OV-Tech-GmbH/OVT13/01_Electronics/01_Keyboard/KB-PCB-R02/OUTPUT/Layerstack Keyboard_JLCPB.png

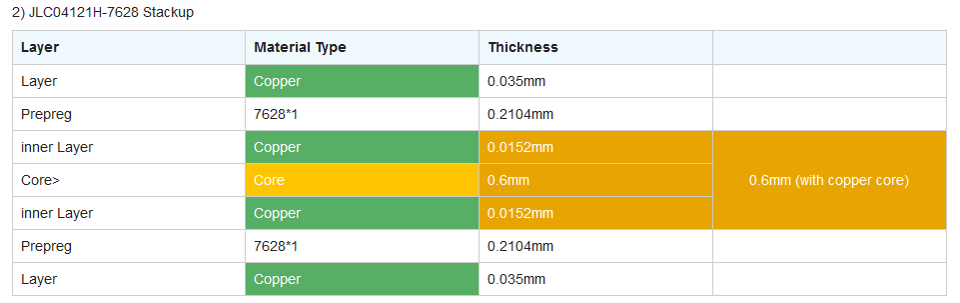
01_Electronics/01_Keyboard/KB-PCB-R02/OUTPUT/Layerstack Keyboard_JLCPB.png
