OV-Tech-GmbH/OVT13/01_Electronics/02_Webcam/KiCad WCAM-TK-PCB-R02/ALTIUM_EMBEDDED_MODELS/ABLS-PCB-R01.stp

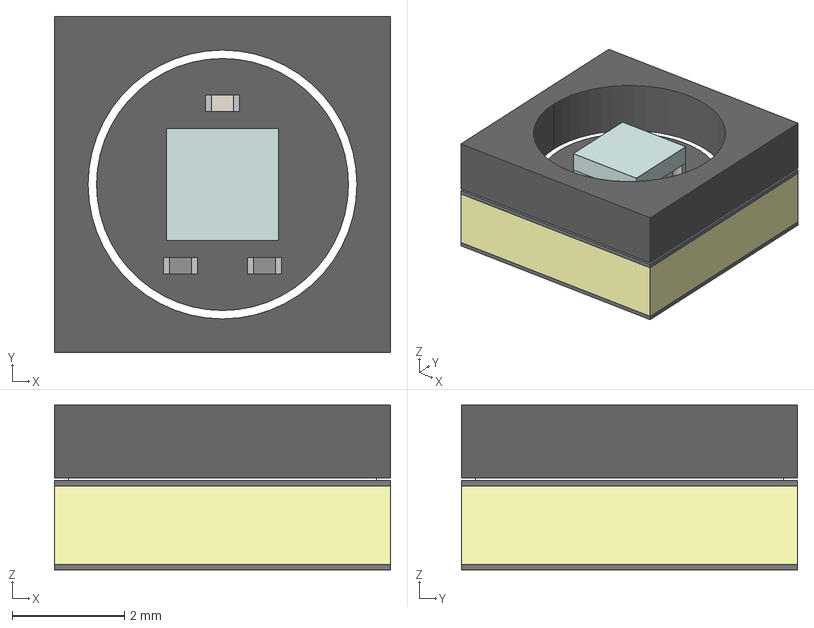
[picture p17: CAD file, 2024-03-24]
01_Electronics/02_Webcam/KiCad WCAM-TK-PCB-R02/ALTIUM_EMBEDDED_MODELS/ABLS-PCB-R01.stp
6.00 x 6.00 x 2.94 mm
ABLS-PCB-R01
IC
Carrier
Verguss
Dampener
