OV-Tech-GmbH/OVT13/01_Electronics/02_Webcam/WCAM-BREAKOUT-PCB-R03/PCB/ALTIUM_EMBEDDED_MODELS/SOT95P275X110-5N.step

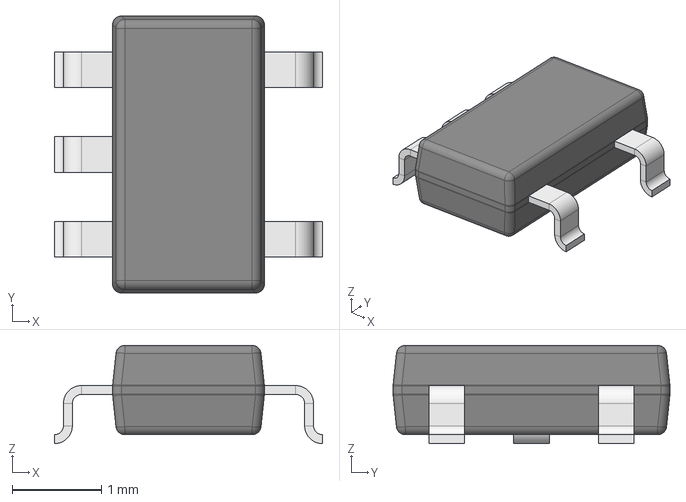
[picture p18: CAD file, 2026-06-02]
01_Electronics/02_Webcam/WCAM-BREAKOUT-PCB-R03/PCB/ALTIUM_EMBEDDED_MODELS/SOT95P275X110-5N.step
3.00 x 3.10 x 1.10 mm
Leader x 5
