OV-Tech-GmbH/OVT13/01_Electronics/02_Webcam/WCAM-TK-PCB-R02/MCAD EXCHANGE/WCAM-PCB-Outline.dxf

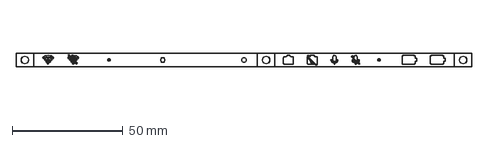
[picture p19: CAD file, 2024-03-02]
01_Electronics/02_Webcam/WCAM-TK-PCB-R02/MCAD EXCHANGE/WCAM-PCB-Outline.dxf
206.0 x 6.00 mm
