OV-Tech-GmbH/OVT13/01_Electronics/03_Trackpad/Trackpad sensor evaluation/TP-EVALBOARD-R01_KiCad/ALTIUM_EMBEDDED_MODELS/USON8_200X300P50.stp

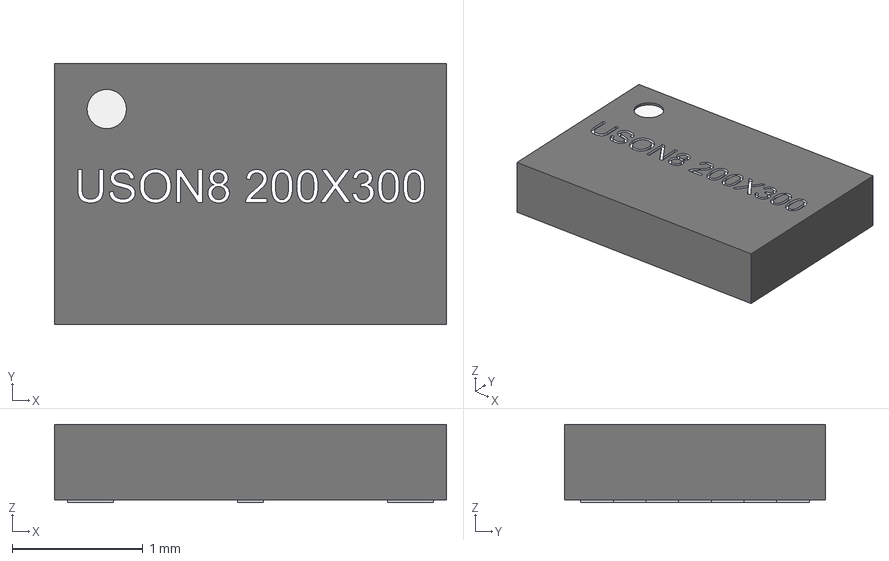
[picture p20: CAD file, 2024-07-25]
01_Electronics/03_Trackpad/Trackpad sensor evaluation/TP-EVALBOARD-R01_KiCad/ALTIUM_EMBEDDED_MODELS/USON8_200X300P50.stp
3.00 x 2.00 x 0.6 mm
