OV-Tech-GmbH/OVT13/01_Electronics/01_Keyboard/KB-PCB-R02_KiCad/ALTIUM_EMBEDDED_MODELS/0603 Chip SMD LED (1.6x0.8mm).STEP

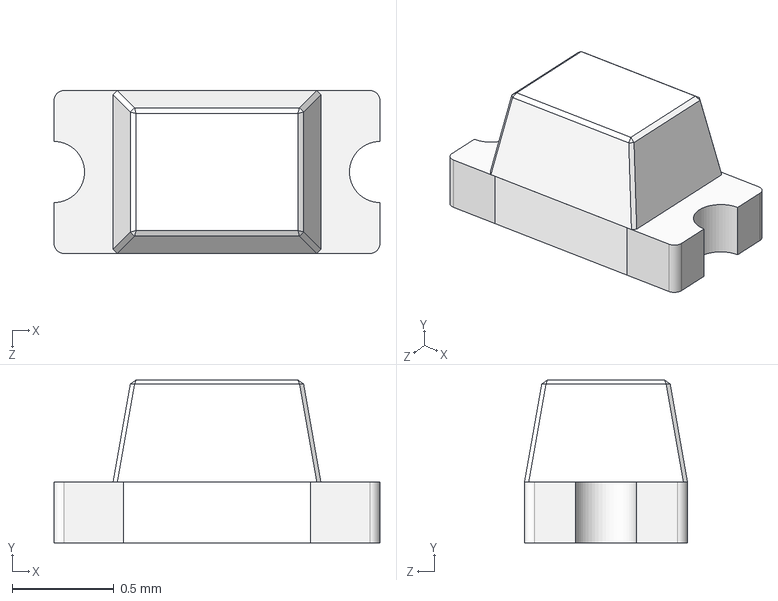
[picture p21: CAD file, 2024-03-24]
01_Electronics/01_Keyboard/KB-PCB-R02_KiCad/ALTIUM_EMBEDDED_MODELS/0603 Chip SMD LED (1.6x0.8mm).STEP
1.60 x 0.8 x 0.8 mm
