OV-Tech-GmbH/OVT13/01_Electronics/02_Webcam/KiCad WCAM-TK-PCB-R02/ALTIUM_EMBEDDED_MODELS/SOT886.stp

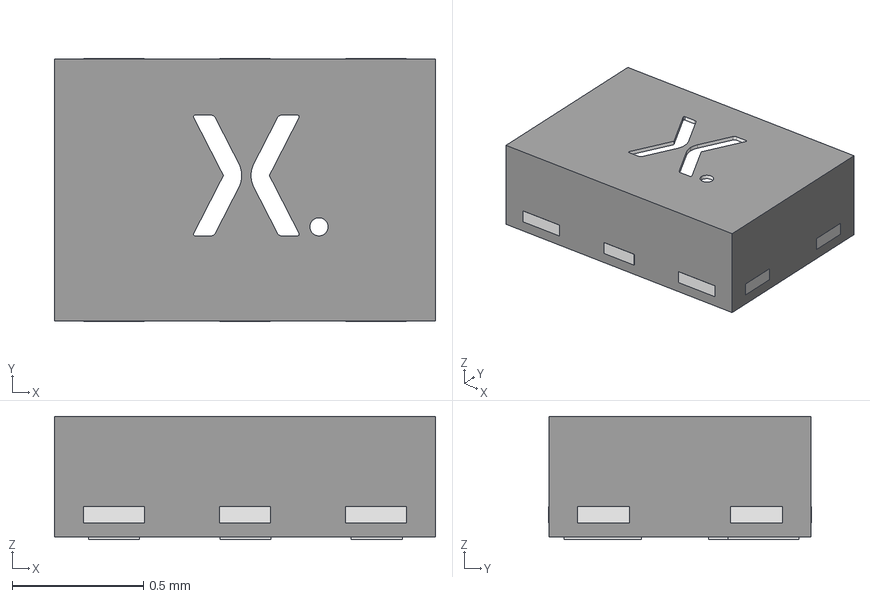
[picture p22: CAD file, 2024-03-24]
01_Electronics/02_Webcam/KiCad WCAM-TK-PCB-R02/ALTIUM_EMBEDDED_MODELS/SOT886.stp
1.45 x 1.00 x 0.47 mm
SOT886 LF
SOT886 Mold Body
