OV-Tech-GmbH/OVT13/01_Electronics/02_Webcam/WCAM-BREAKOUT-PCB-R03/PCB/ALTIUM_EMBEDDED_MODELS/CAF-50P85X64-4N.step

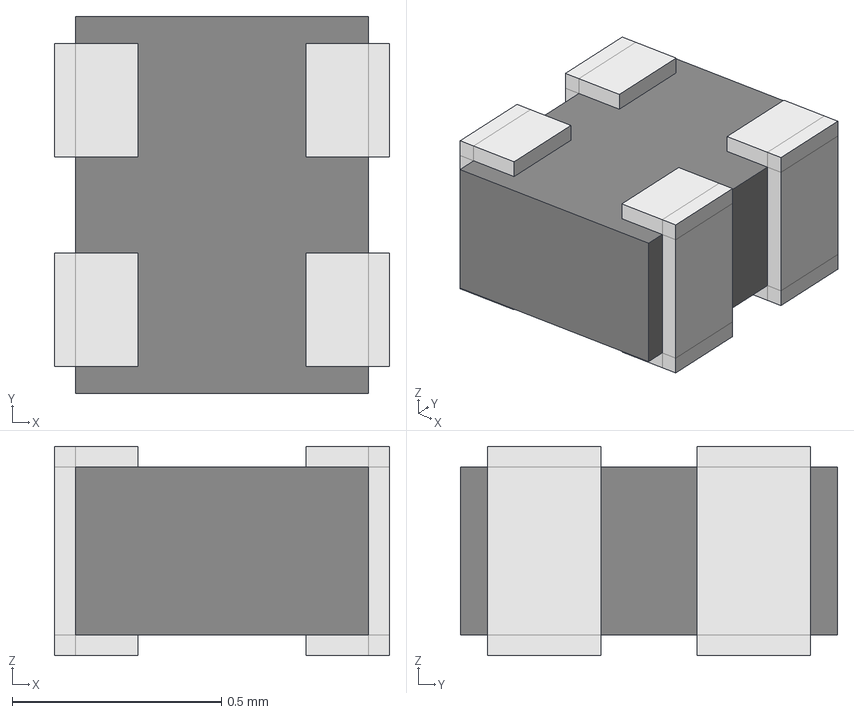
[picture p23: CAD file, 2026-06-02]
01_Electronics/02_Webcam/WCAM-BREAKOUT-PCB-R03/PCB/ALTIUM_EMBEDDED_MODELS/CAF-50P85X64-4N.step
0.8 x 0.9 x 0.5 mm
