OV-Tech-GmbH/OVT13/01_Electronics/03_Trackpad/Trackpad sensor evaluation/TP-EVALBOARD-R01_KiCad/ALTIUM_EMBEDDED_MODELS/Crystal_250X200X60.stp

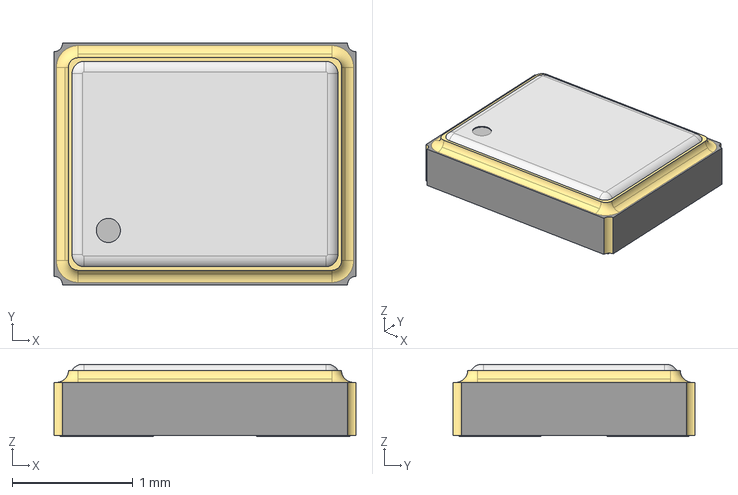
[picture p24: CAD file, 2024-07-25]
01_Electronics/03_Trackpad/Trackpad sensor evaluation/TP-EVALBOARD-R01_KiCad/ALTIUM_EMBEDDED_MODELS/Crystal_250X200X60.stp
2.50 x 2.00 x 0.6 mm
