OV-Tech-GmbH/OVT13/01_Electronics/01_Keyboard/KB-PCB-R02_KiCad/ALTIUM_EMBEDDED_MODELS/MPL-AL4020-xxx.STEP

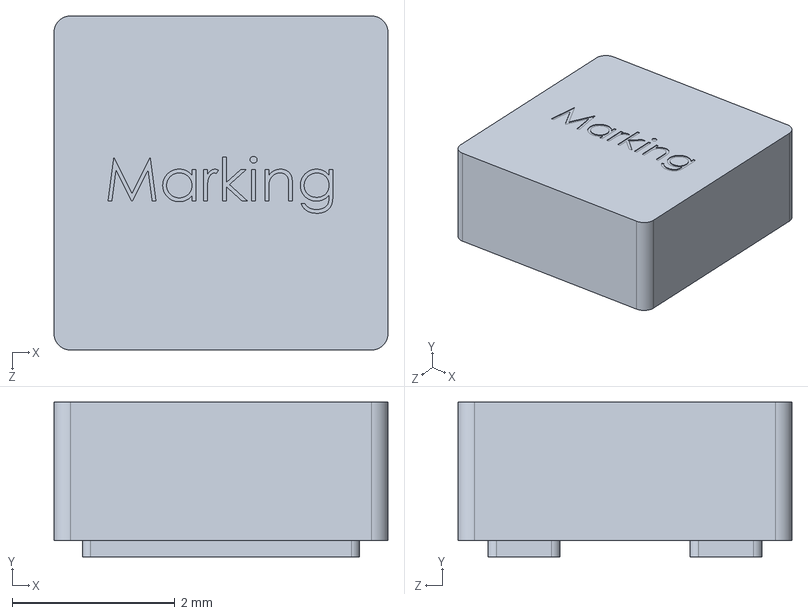
[picture p25: CAD file, 2024-03-24]
01_Electronics/01_Keyboard/KB-PCB-R02_KiCad/ALTIUM_EMBEDDED_MODELS/MPL-AL4020-xxx.STEP
4.10 x 1.90 x 4.10 mm
