OV-Tech-GmbH/OVT13/01_Electronics/02_Webcam/KiCad WCAM-TK-PCB-R02/ALTIUM_EMBEDDED_MODELS/EMI Shielding Spring Contact 3-2199250-3.stp

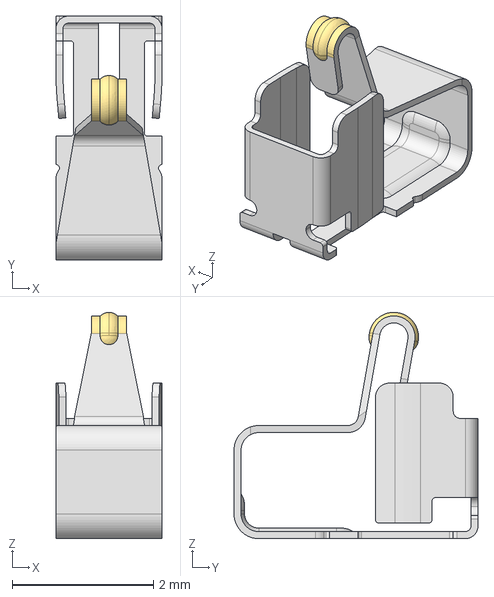
[picture p26: CAD file, 2024-03-24]
01_Electronics/02_Webcam/KiCad WCAM-TK-PCB-R02/ALTIUM_EMBEDDED_MODELS/EMI Shielding Spring Contact 3-2199250-3.stp
1.50 x 3.45 x 3.20 mm
