OV-Tech-GmbH/OVT13/01_Electronics/02_Webcam/WCAM-BREAKOUT-PCB-R03/PCB/ALTIUM_EMBEDDED_MODELS/F32Q-1A7H1-11015--3DModel-STEP-56544.STEP

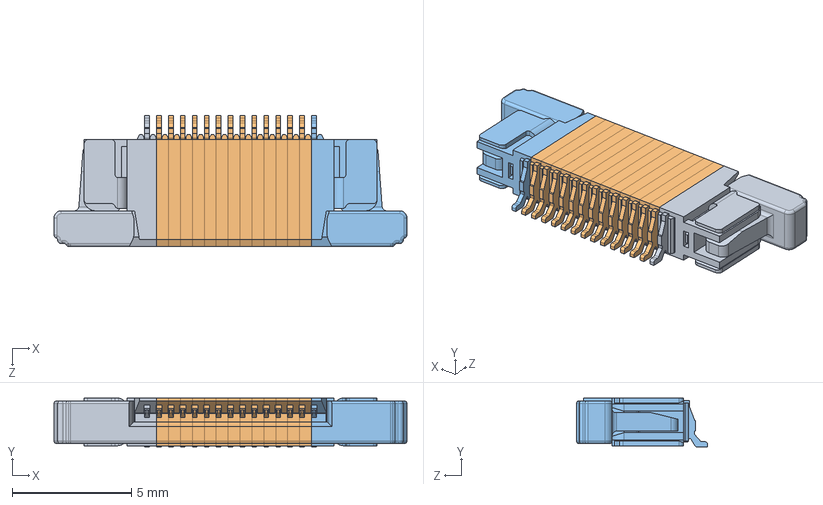
[picture p27: CAD file, 2026-06-02]
01_Electronics/02_Webcam/WCAM-BREAKOUT-PCB-R03/PCB/ALTIUM_EMBEDDED_MODELS/F32Q-1A7H1-11015--3DModel-STEP-56544.STEP
14.8 x 2.05 x 5.50 mm
F32Q_L.STEP
F32Q_M.STEP x 13
F32Q_R.STEP
