OV-Tech-GmbH/OVT13/01_Electronics/03_Trackpad/Trackpad sensor evaluation/TP-EVALBOARD-R01_KiCad/ALTIUM_EMBEDDED_MODELS/PTS815SJM250SMTRLFS.stp

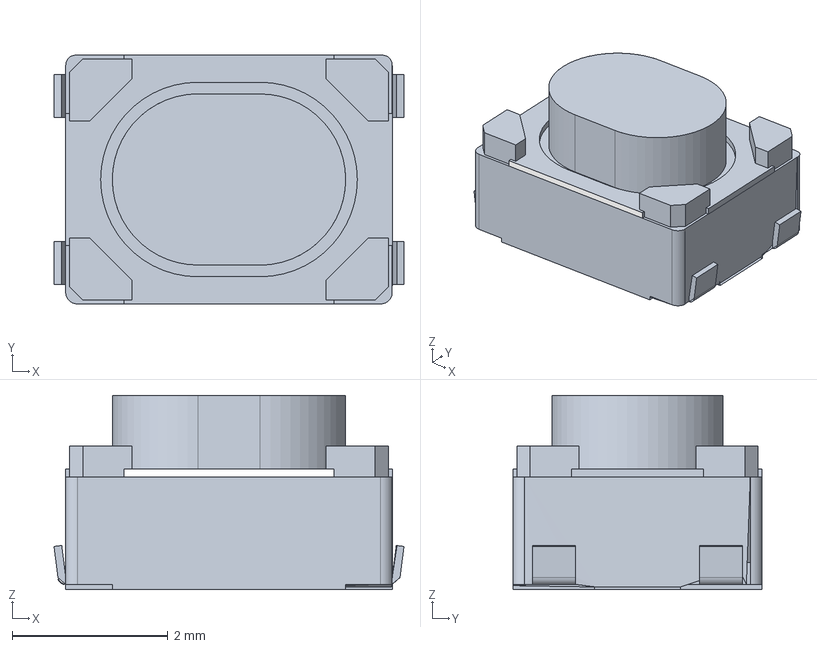
[picture p28: CAD file, 2024-07-25]
01_Electronics/03_Trackpad/Trackpad sensor evaluation/TP-EVALBOARD-R01_KiCad/ALTIUM_EMBEDDED_MODELS/PTS815SJM250SMTRLFS.stp
4.50 x 3.20 x 2.50 mm
PTS815SJM250SMTRLFS_PART3
PTS815SJM250SMTRLFS_PART2
PTS815SJM250SMTRLFS_PART1
