OV-Tech-GmbH/OVT13/01_Electronics/01_Keyboard/KB-PCB-R02_KiCad/ALTIUM_EMBEDDED_MODELS/QFN40P700X700X90_HS-57M.step

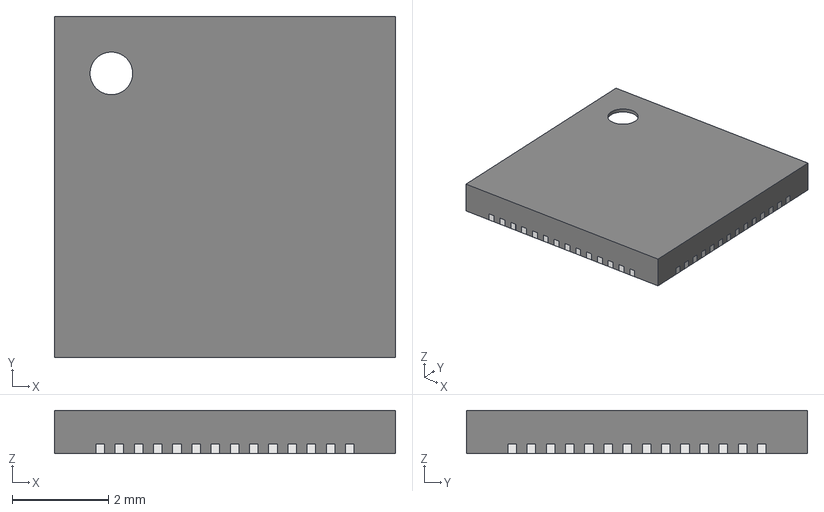
[picture p29: CAD file, 2024-03-24]
01_Electronics/01_Keyboard/KB-PCB-R02_KiCad/ALTIUM_EMBEDDED_MODELS/QFN40P700X700X90_HS-57M.step
7.10 x 7.10 x 0.901 mm
Thermal Shape
