OV-Tech-GmbH/OVT13/01_Electronics/02_Webcam/KiCad WCAM-TK-PCB-R02/ALTIUM_EMBEDDED_MODELS/SOT23-6-2.step

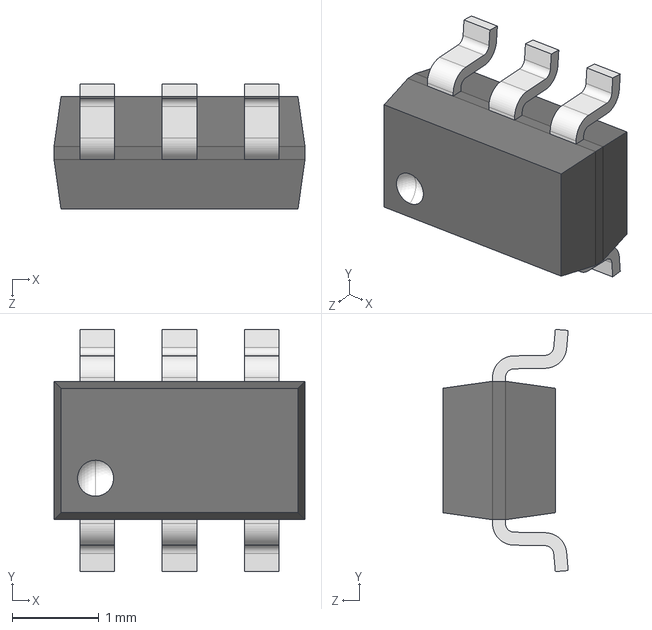
[picture p30: CAD file, 2024-03-24]
01_Electronics/02_Webcam/KiCad WCAM-TK-PCB-R02/ALTIUM_EMBEDDED_MODELS/SOT23-6-2.step
2.90 x 2.80 x 1.45 mm
