OV-Tech-GmbH/OVT13/01_Electronics/02_Webcam/WCAM-BREAKOUT-PCB-R03/PCB/ALTIUM_EMBEDDED_MODELS/TSOP65P280X110-8N.step

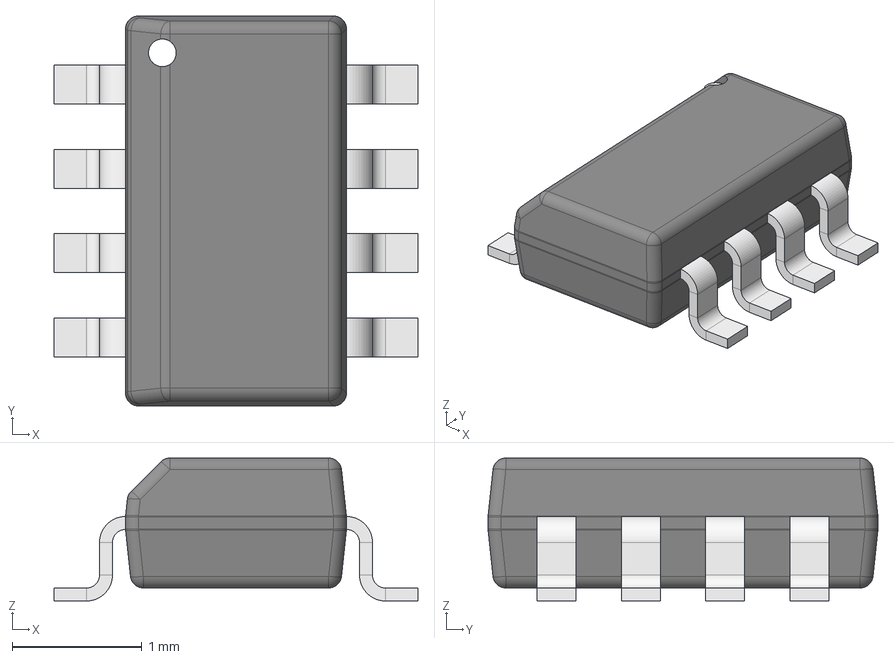
[picture p31: CAD file, 2026-06-02]
01_Electronics/02_Webcam/WCAM-BREAKOUT-PCB-R03/PCB/ALTIUM_EMBEDDED_MODELS/TSOP65P280X110-8N.step
2.80 x 3.00 x 1.10 mm
Leader x 8
