OV-Tech-GmbH/OVT13/01_Electronics/01_Keyboard/KB-PCB-R02_KiCad/ALTIUM_EMBEDDED_MODELS/ECS-143-18-30BQ-DS.STEP

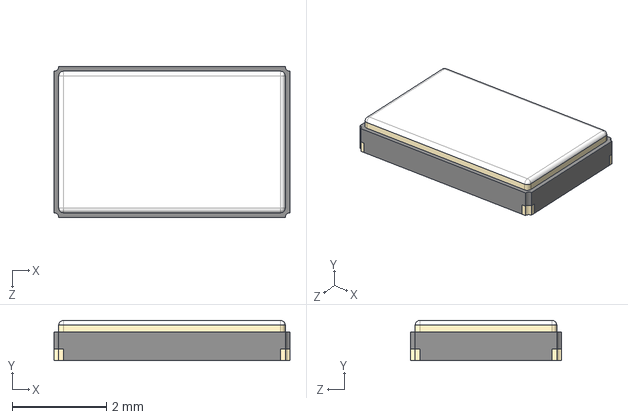
[picture p32: CAD file, 2024-03-24]
01_Electronics/01_Keyboard/KB-PCB-R02_KiCad/ALTIUM_EMBEDDED_MODELS/ECS-143-18-30BQ-DS.STEP
5.00 x 0.85 x 3.20 mm
