OV-Tech-GmbH/OVT13/01_Electronics/02_Webcam/KiCad WCAM-TK-PCB-R02/ALTIUM_EMBEDDED_MODELS/LED_Diffusor.stp

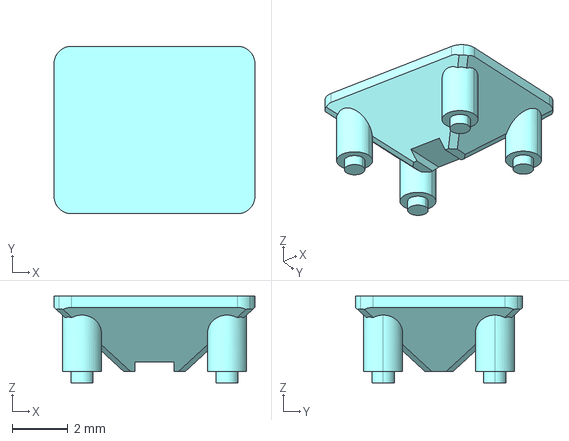
[picture p33: CAD file, 2024-03-24]
01_Electronics/02_Webcam/KiCad WCAM-TK-PCB-R02/ALTIUM_EMBEDDED_MODELS/LED_Diffusor.stp
7.20 x 6.00 x 3.10 mm
