OV-Tech-GmbH/OVT13/01_Electronics/01_Keyboard/KB-PCB-R02_KiCad/ALTIUM_EMBEDDED_MODELS/RES_0603_m1608.stp

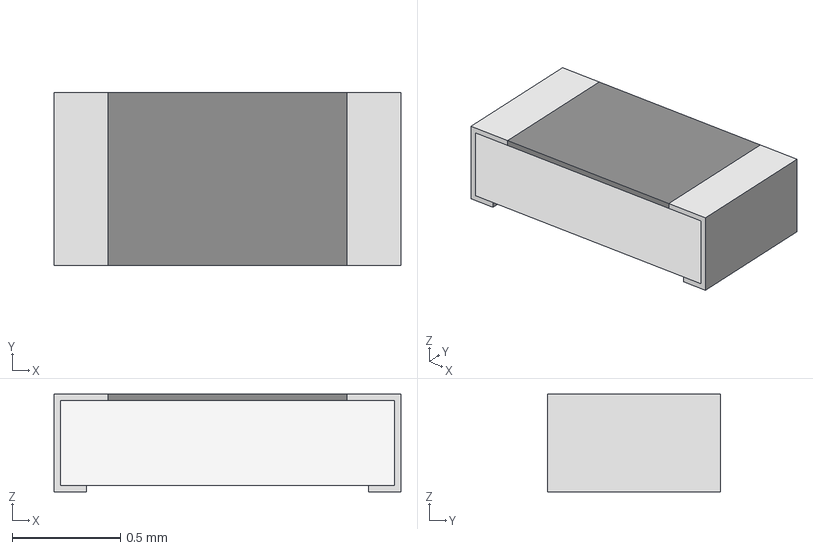
[picture p34: CAD file, 2024-03-24]
01_Electronics/01_Keyboard/KB-PCB-R02_KiCad/ALTIUM_EMBEDDED_MODELS/RES_0603_m1608.stp
1.60 x 0.8 x 0.45 mm
