OV-Tech-GmbH/OVT13/01_Electronics/02_Webcam/KiCad WCAM-TK-PCB-R02/ALTIUM_EMBEDDED_MODELS/WCAM-MOUNT-PCB-R01.step

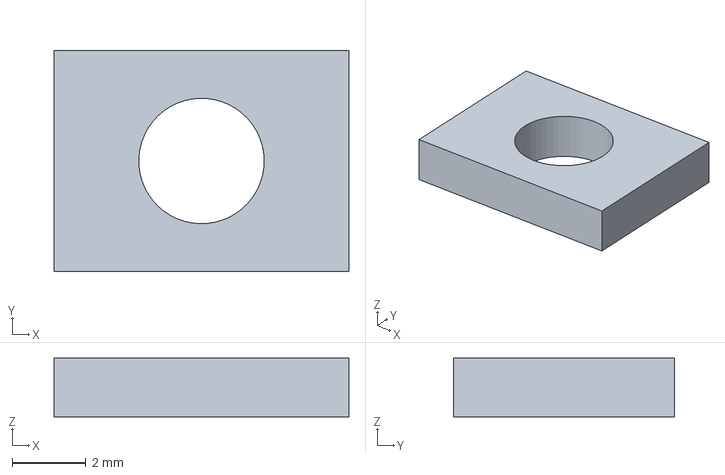
[picture p35: CAD file, 2024-03-02]
01_Electronics/02_Webcam/KiCad WCAM-TK-PCB-R02/ALTIUM_EMBEDDED_MODELS/WCAM-MOUNT-PCB-R01.step
8.00 x 6.00 x 1.59 mm
