OV-Tech-GmbH/OVT13/01_Electronics/03_Trackpad/Trackpad sensor evaluation/TP-EVALBOARD-R01_KiCad/ALTIUM_EMBEDDED_MODELS/User Library-JST - SM05B-SRSS-TB (SH SERIES - 1_0mm PITCH WIRE-TO-BOARD, SMT, RA).step

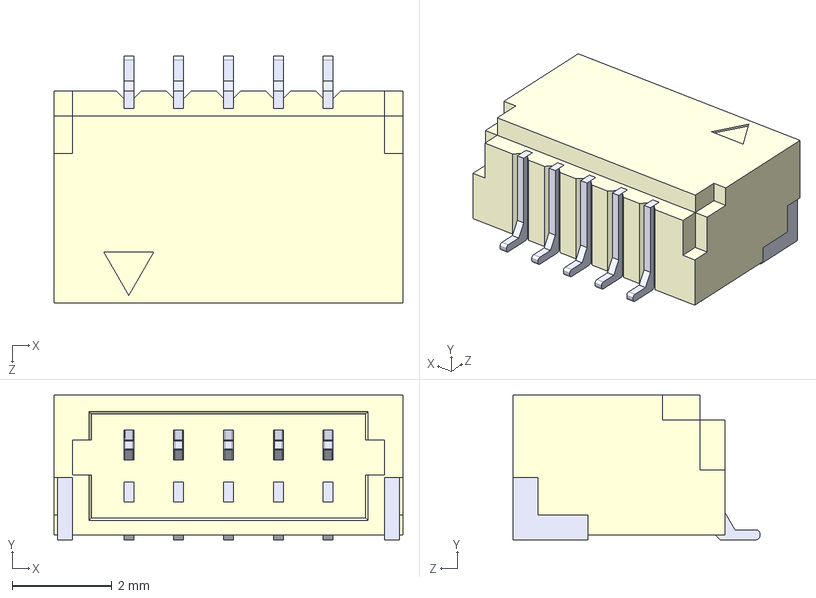
[picture p36: CAD file, 2024-03-24]
01_Electronics/03_Trackpad/Trackpad sensor evaluation/TP-EVALBOARD-R01_KiCad/ALTIUM_EMBEDDED_MODELS/User Library-JST - SM05B-SRSS-TB (SH SERIES - 1_0mm PITCH WIRE-TO-BOARD, SMT, RA).step
7.00 x 2.90 x 4.95 mm
