OV-Tech-GmbH/OVT13/01_Electronics/02_Webcam/KiCad WCAM-TK-PCB-R02/ALTIUM_EMBEDDED_MODELS/3D Model Mic Dampener.stp

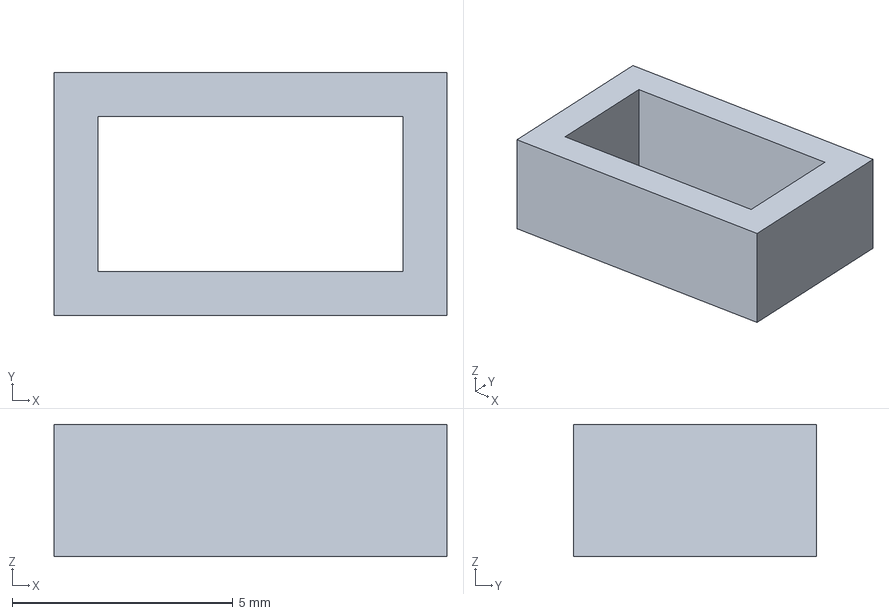
[picture p37: CAD file, 2024-03-02]
01_Electronics/02_Webcam/KiCad WCAM-TK-PCB-R02/ALTIUM_EMBEDDED_MODELS/3D Model Mic Dampener.stp
8.90 x 5.50 x 3.00 mm
