OV-Tech-GmbH/OVT13/01_Electronics/02_Webcam/WCAM-BREAKOUT-PCB-R03/PCB/ALTIUM_EMBEDDED_MODELS/X2SON 1x1x0.4.stp

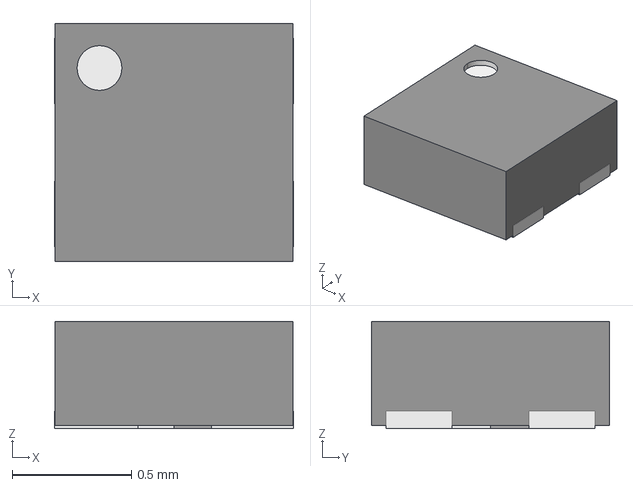
[picture p38: CAD file, 2024-03-24]
01_Electronics/02_Webcam/WCAM-BREAKOUT-PCB-R03/PCB/ALTIUM_EMBEDDED_MODELS/X2SON 1x1x0.4.stp
1.00 x 1.00 x 0.45 mm
