OV-Tech-GmbH/OVT13/01_Electronics/03_Trackpad/Trackpad sensor evaluation/TP-EVALBOARD-R01_KiCad/ALTIUM_EMBEDDED_MODELS/CAP_0603_m1608.stp

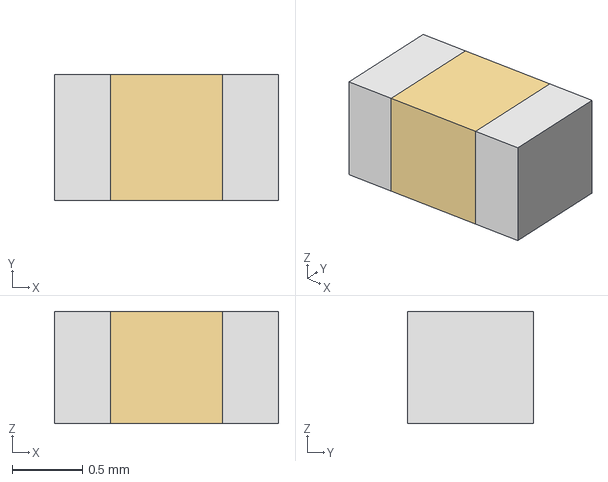
[picture p39: CAD file, 2024-03-24]
01_Electronics/03_Trackpad/Trackpad sensor evaluation/TP-EVALBOARD-R01_KiCad/ALTIUM_EMBEDDED_MODELS/CAP_0603_m1608.stp
1.60 x 0.9 x 0.8 mm
