OV-Tech-GmbH/OVT13/01_Electronics/01_Keyboard/KB-PCB-R02_KiCad/ALTIUM_EMBEDDED_MODELS/CPG1316S01D02.2.stp

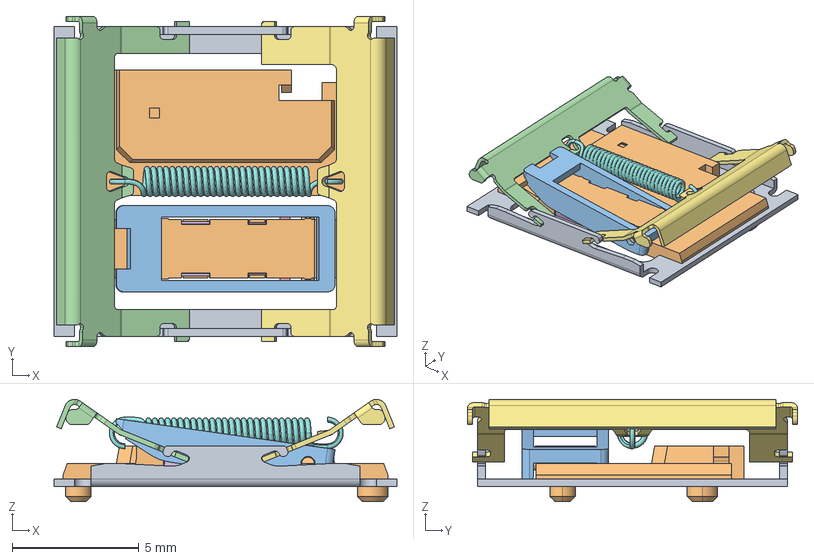
[picture p40: CAD file, 2024-03-24]
01_Electronics/01_Keyboard/KB-PCB-R02_KiCad/ALTIUM_EMBEDDED_MODELS/CPG1316S01D02.2.stp
13.5 x 13.0 x 4.03 mm
Base
Base_Plastic
Switch_Lever
Lever_2
Stabilizer_1
Stabilizer_2
Lever_1
Spring
