OV-Tech-GmbH/OVT13/01_Electronics/02_Webcam/WCAM-BREAKOUT-PCB-R03/PCB/ALTIUM_EMBEDDED_MODELS/Image Sensor OV2740.stp

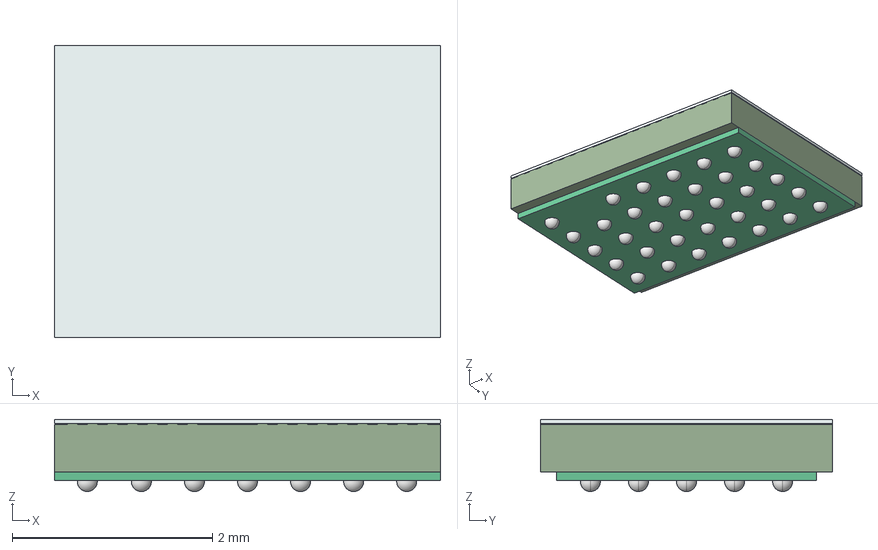
[picture p41: CAD file, 2024-03-24]
01_Electronics/02_Webcam/WCAM-BREAKOUT-PCB-R03/PCB/ALTIUM_EMBEDDED_MODELS/Image Sensor OV2740.stp
3.85 x 2.92 x 0.72 mm
Cover
Base
Balls
