OV-Tech-GmbH/OVT13/01_Electronics/01_Keyboard/KB-PCB-R02_KiCad/ALTIUM_EMBEDDED_MODELS/SON50P300X60_HS-9N.step

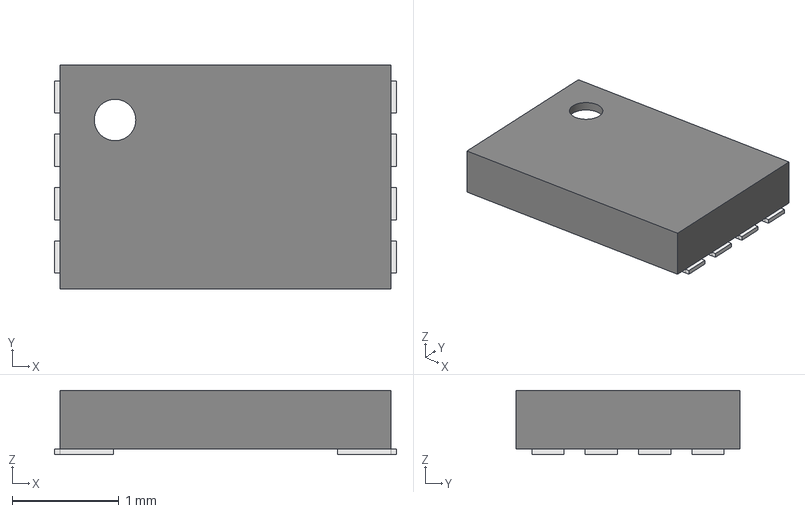
[picture p42: CAD file, 2024-03-24]
01_Electronics/01_Keyboard/KB-PCB-R02_KiCad/ALTIUM_EMBEDDED_MODELS/SON50P300X60_HS-9N.step
3.20 x 2.10 x 0.6 mm
