OV-Tech-GmbH/OVT13/01_Electronics/02_Webcam/WCAM-BREAKOUT-PCB-R03/PCB/ALTIUM_EMBEDDED_MODELS/Oscillator ECS-2520MV.stp

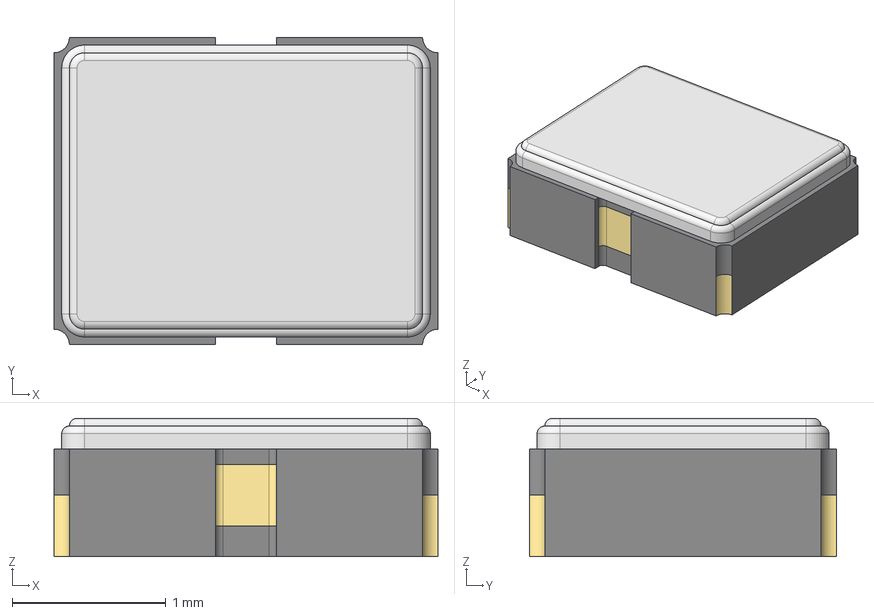
[picture p43: CAD file, 2024-03-24]
01_Electronics/02_Webcam/WCAM-BREAKOUT-PCB-R03/PCB/ALTIUM_EMBEDDED_MODELS/Oscillator ECS-2520MV.stp
2.50 x 2.00 x 0.9 mm
