OV-Tech-GmbH/OVT13/01_Electronics/02_Webcam/WCAM-BREAKOUT-PCB-R03/PCB/ALTIUM_EMBEDDED_MODELS/DFN65P98X50-3N.step

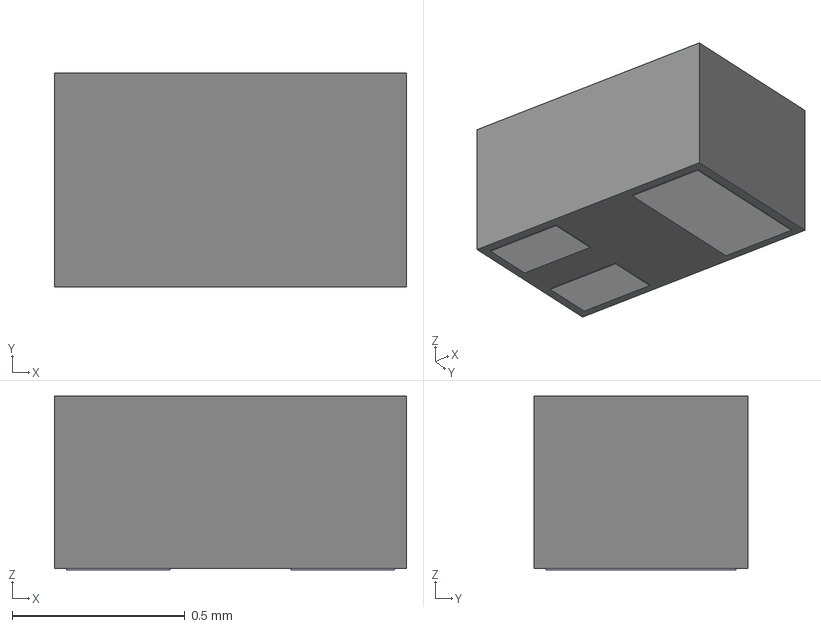
[picture p44: CAD file, 2024-03-24]
01_Electronics/02_Webcam/WCAM-BREAKOUT-PCB-R03/PCB/ALTIUM_EMBEDDED_MODELS/DFN65P98X50-3N.step
1.02 x 0.62 x 0.503 mm
bigPin
smallPine x 2
