OV-Tech-GmbH/OVT13/01_Electronics/02_Webcam/WCAM-BREAKOUT-PCB-R03/PCB/ALTIUM_EMBEDDED_MODELS/DFN65P100X50-2N.step

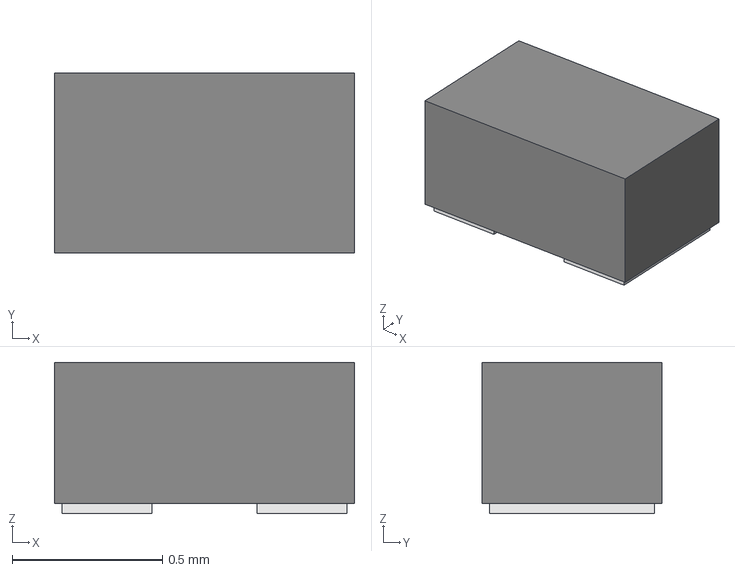
[picture p45: CAD file, 2024-03-24]
01_Electronics/02_Webcam/WCAM-BREAKOUT-PCB-R03/PCB/ALTIUM_EMBEDDED_MODELS/DFN65P100X50-2N.step
1.00 x 0.6 x 0.503 mm
bigPin x 2
