OV-Tech-GmbH/OVT13/01_Electronics/02_Webcam/WCAM-BREAKOUT-PCB-R01/OUTPUT/Lagenaufbau Keyboard_JLCPB.png

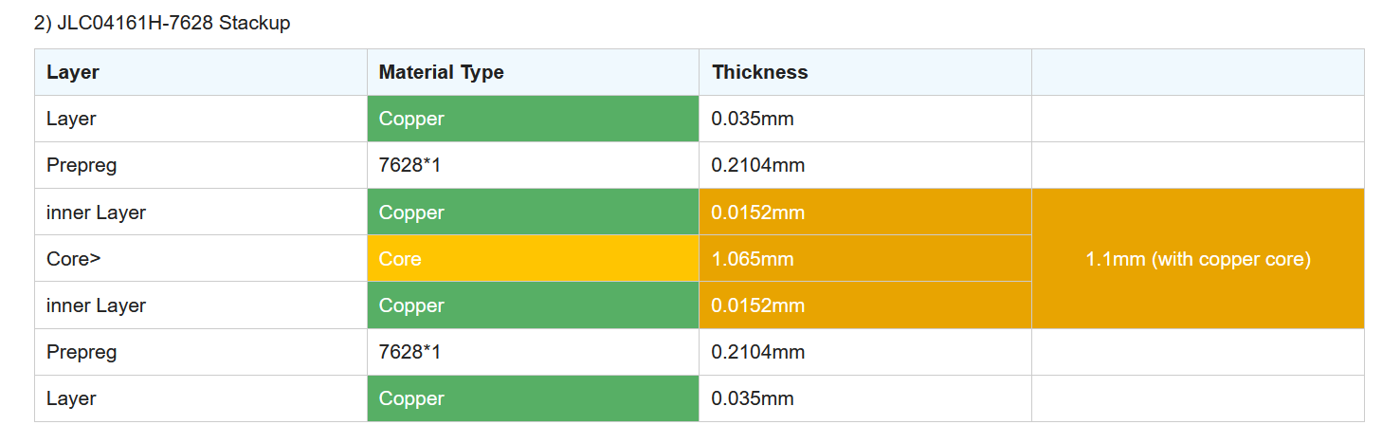
01_Electronics/02_Webcam/WCAM-BREAKOUT-PCB-R01/OUTPUT/Lagenaufbau Keyboard_JLCPB.png
