OV-Tech-GmbH/OVT13/01_Electronics/01_Keyboard/KB-PCB-R02_KiCad/Input_MCU.kicad_sch

## KiCad design 01_Electronics/01_Keyboard/KB-PCB-R02_KiCad/Input_MCU.kicad_sch (2024-03-24)

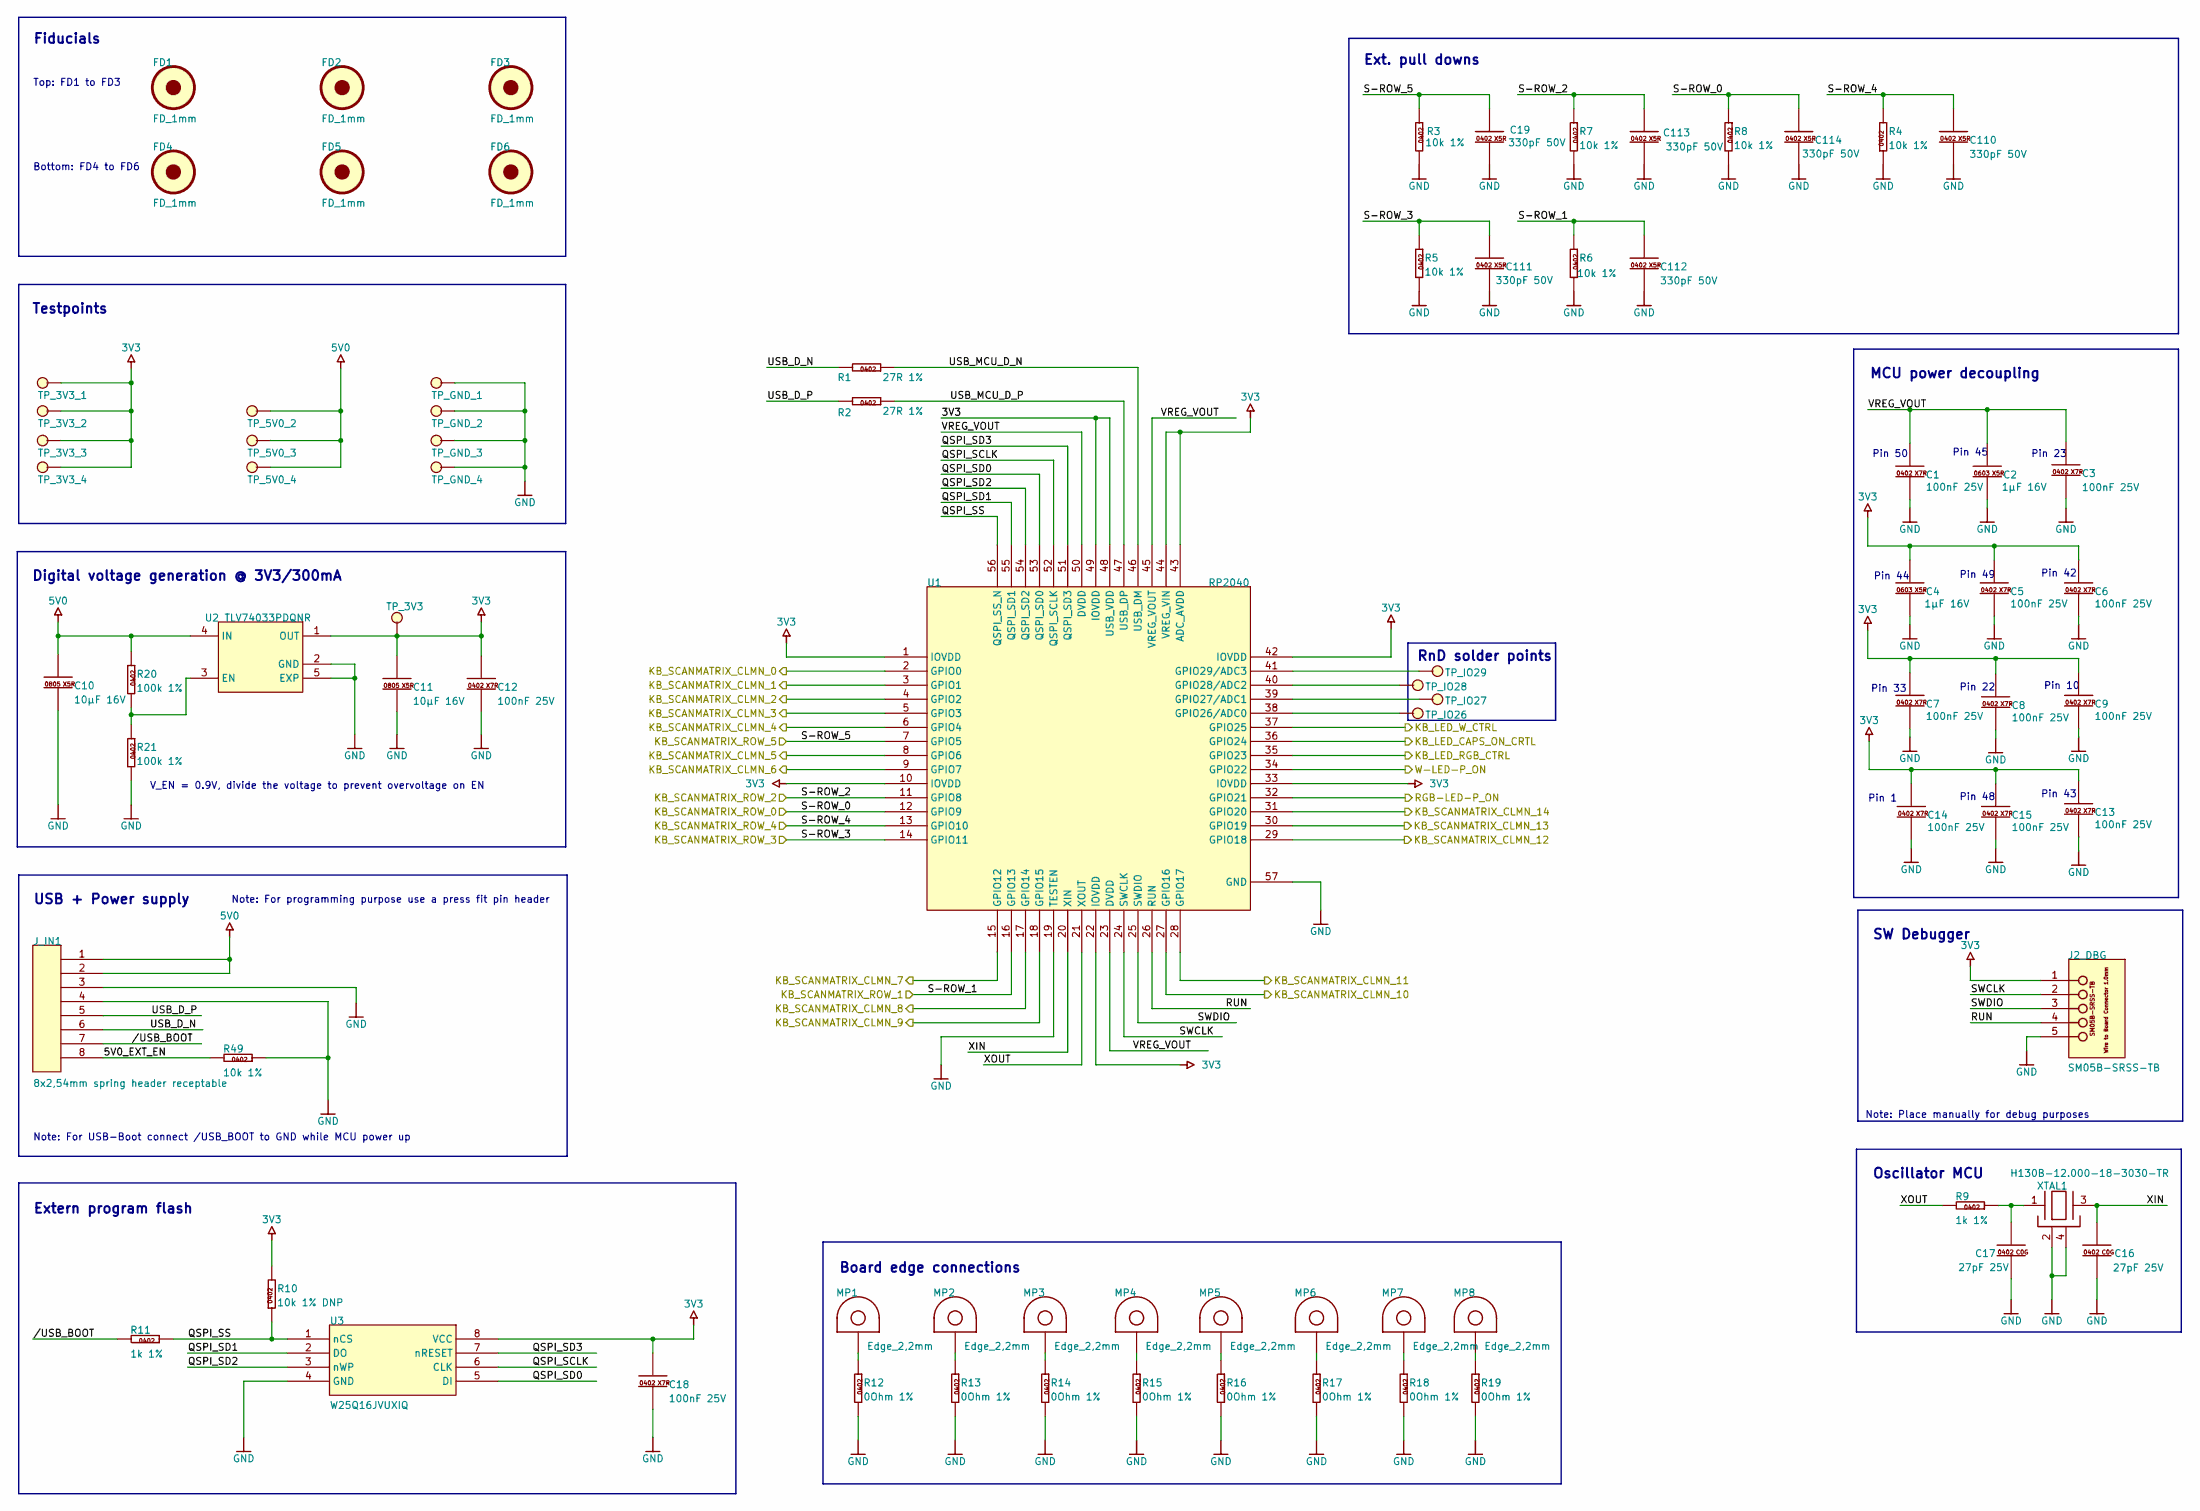
[picture p61: schematic Input_MCU.kicad_sch]

Parts:
C1, C3, C5, C6, C7, C8, C9, C12, C13, C14, C15, C18: 100nF 25V; CAPC1005X06L
C2, C4: 1µF 16V; CAPC1608X10L
C10, C11: 10µF 16V; CAPC2012X14L
C16, C17: 27pF 25V; CAPC1005X06L
C19, C110, C111, C112, C113, C114: 330pF 50V; CAPC1005X06L
FD1, FD2, FD3, FD4, FD5, FD6: FD_1mm; FD_1mm_Copper_3mm_Expansion
J2_DBG: SM05B-SRSS-TB; Wire-to-Board SM05B-SRSS-TB
J_IN1: 8x2,54mm spring header receptable; BOARD-BOARD CON SPRING-LOADED HEADER 8x2,54mm Receptable; MANUFACTURER PART NUMBE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 N/A
MP1, MP2, MP3, MP4, MP5, MP6, MP7, MP8: Edge_2,2mm; MP_Keyboard_EdgeMounts_2.2mm
R1, R2: 27R 1%; RESC1005X04L
R3, R4, R5, R6, R7, R8, R49: 10k 1%; RESC1005X04L
R9, R11: 1k 1%; RESC1005X04L
R10: 10k 1% DNP; RESC1005X04L
R12, R13, R14, R15, R16, R17, R18, R19: 0Ohm 1%; RESC1005X04L
R20, R21: 100k 1%; RESC1005X04L
TP_3V3, TP_3V3_1, TP_3V3_2, TP_3V3_3, TP_3V3_4, TP_5V0_2, TP_5V0_3, TP_5V0_4: Testpoint 0.75mm; TP_0.75mm
TP_GND_1, TP_GND_2, TP_GND_3, TP_GND_4: Testpoint 0.75mm; TP_0.75mm
TP_IO26, TP_IO27, TP_IO28, TP_IO29: Testpoint 0.75mm; TP_0.75mm
U1: RP2040; QFN40P700X700X90_HS-57M
U2: TLV74033PDQNR; X2SON-DFN
U3: W25Q16JVUXIQ; SON50P300X60_HS-9N; MANUFACTURER PART NUMBE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 W25Q16JVUXIQ
XTAL1: H130B-12.000-18-3030-TR; XTAL_H130B-12.000-18-3030-TR

Connections:
3V3: U1.48 (USB_VDD), U1.49 (IOVDD)
5V0_EXT_EN: J_IN1.8, R49.1
/USB_BOOT: J_IN1.7, R11.1
KB_LED_CAPS_ON_CRTL: U1.36 (GPIO24)
KB_LED_RGB_CTRL: U1.35 (GPIO23)
KB_LED_W_CTRL: U1.37 (GPIO25)
KB_SCANMATRIX_CLMN_0: U1.2 (GPIO0)
KB_SCANMATRIX_CLMN_1: C19.1, C111.1, R3.2, R5.2, U1.3 (GPIO1), U1.4 (GPIO2), U1.5 (GPIO3), U1.7 (GPIO5), U1.9 (GPIO7), U1.14 (GPIO11), U1.15 (GPIO12), U1.17 (GPIO14), U1.18 (GPIO15)
KB_SCANMATRIX_CLMN_4: U1.6 (GPIO4)
KB_SCANMATRIX_CLMN_5: U1.8 (GPIO6)
KB_SCANMATRIX_CLMN_10: U1.27 (GPIO16)
KB_SCANMATRIX_CLMN_11: U1.28 (GPIO17)
KB_SCANMATRIX_CLMN_12: U1.29 (GPIO18)
KB_SCANMATRIX_CLMN_13: U1.30 (GPIO19)
KB_SCANMATRIX_CLMN_14: U1.31 (GPIO20)
KB_SCANMATRIX_ROW_0: C114.1, R8.2, U1.12 (GPIO9)
KB_SCANMATRIX_ROW_1: C112.1, R6.2, U1.16 (GPIO13)
KB_SCANMATRIX_ROW_2: C113.1, R7.2, U1.11 (GPIO8)
KB_SCANMATRIX_ROW_4: C110.1, R4.1, U1.13 (GPIO10)
unnamed: C4.1, C5.1, C6.1
unnamed: C7.1, C8.1, C9.1
unnamed: C10.1, R20.2, U2.4 (IN)
unnamed: C11.1, C12.1, TP_3V3.TP, U2.1 (OUT)
unnamed: C13.1, C14.1, C15.1
unnamed: C17.1, R9.2, XTAL1.1
unnamed: C18.1, U3.8 (VCC)
unnamed: J_IN1.1, J_IN1.2
unnamed: J_IN1.4, R49.2
unnamed: MP1.1, R12.2
unnamed: MP2.1, R13.2
unnamed: MP3.1, R14.2
unnamed: MP4.1, R15.2
unnamed: MP5.1, R16.2
unnamed: MP6.1, R17.2
unnamed: MP7.1, R18.2
unnamed: MP8.1, R19.2
unnamed: R20.1, R21.2, U2.3 (EN)
unnamed: TP_3V3_1.TP, TP_3V3_2.TP, TP_3V3_3.TP, TP_3V3_4.TP
unnamed: TP_5V0_2.TP, TP_5V0_3.TP, TP_5V0_4.TP
unnamed: TP_GND_1.TP, TP_GND_2.TP, TP_GND_3.TP, TP_GND_4.TP
unnamed: TP_IO26.TP, U1.38 (GPIO26/ADC0)
unnamed: TP_IO27.TP, U1.39 (GPIO27/ADC1)
unnamed: TP_IO28.TP, U1.40 (GPIO28/ADC2)
unnamed: TP_IO29.TP, U1.41 (GPIO29/ADC3)
unnamed: U1.43 (ADC_AVDD), U1.44 (VREG_VIN)
unnamed: U2.2 (GND), U2.5 (EXP)
unnamed: XTAL1.2, XTAL1.4
QSPI_SCLK: U1.52 (QSPI_SCLK), U3.6 (CLK)
QSPI_SD0: U1.53 (QSPI_SD0), U3.5 (DI)
QSPI_SD1: U1.55 (QSPI_SD1), U3.2 (DO)
QSPI_SD2: U1.54 (QSPI_SD2), U3.3 (nWP)
QSPI_SD3: U1.51 (QSPI_SD3), U3.7 (nRESET)
QSPI_SS: R10.2, R11.2, U1.56 (QSPI_SS_N), U3.1 (nCS)
RGB-LED-P_ON: U1.32 (GPIO21)
RUN: J2_DBG.4, U1.26 (RUN)
SWCLK: J2_DBG.2, U1.24 (SWCLK)
SWDIO: J2_DBG.3, U1.25 (SWDIO)
USB_D_N: J_IN1.6, R1.1
USB_D_P: J_IN1.5, R2.1
USB_MCU_D_N: R1.2, U1.46 (USB_DM)
USB_MCU_D_P: R2.2, U1.47 (USB_DP)
VREG_VOUT: C1.1, C2.1, C3.1, U1.23 (DVDD), U1.45 (VREG_VOUT), U1.50 (DVDD)
W-LED-P_ON: U1.34 (GPIO22)
XIN: C16.1, U1.20 (XIN), XTAL1.3
XOUT: R9.1, U1.21 (XOUT)

Notes on the sheet:
Note: For USB-Boot connect /USB_BOOT to GND while MCU power up
Pin 22
USB + Power supply
Top: FD1 to FD3
Pin 49
Pin 33
V_EN = 0.9V, divide the voltage to prevent overvoltage on EN
Note: For programming purpose use a press fit pin header
Pin 48
Ext. pull downs
Board edge connections
Bottom: FD4 to FD6
Testpoints
Pin 23
Pin 44
Extern program flash
Pin 1
Pin 45
Note: Place manually for debug purposes
Pin 42
Pin 43
MCU power decoupling
SW Debugger
Pin 10
Pin 50
RnD solder points
Fiducials
Oscillator MCU
Digital voltage generation @ 3V3/300mA
