OV-Tech-GmbH/OVT13/01_Electronics/01_Keyboard/KB-PCB-R02_KiCad/Keymatrix_switches.kicad_sch

## KiCad design 01_Electronics/01_Keyboard/KB-PCB-R02_KiCad/Keymatrix_switches.kicad_sch (2024-03-24)

Schematic: Keymatrix_switches.kicad_sch

Parts:
D1, D2, D3, D4, D5, D6, D7, D8, D9, D10, D11, D12, D13, D14, D15, D16, D17, D18, D19, D20, D21, D22, D23, D24, D25, D26, D27, D28, D29, D30, D31, D32, D33, D34, D35, D36, D37, D38, D39, D40, D41, D42, D43, D44, D45, D46, D47, D48, D49, D50, D51, D52, D53, D54, D55, D56, D57, D58, D59, D60, D61, D62, D63, D64, D65, D66, D67, D68, D69, D70, D71, D72, D73, D74, D75, D76, D77, D78, D79, D80: BAT54LS-QYL; DFN1006-2A
D81, D82, D83, D84, D85, D86, D87, D88, D89, D90, D91, D92, D93, D94, D95, D96, D97, D98, D99, D100, D101: PESD5V5C1UL; DFN65P100X50-2N
R147, R148, R149, R150, R151, R152, R153, R154, R155, R156, R157, R158, R159, R160, R161, R162, R163, R164, R165, R166, R167: 300R 1%; RESC1005X04L
SW1, SW2, SW3, SW4, SW5, SW6, SW7, SW8, SW9, SW10, SW11, SW12, SW13, SW14, SW15, SW16, SW17, SW18, SW19, SW20, SW21, SW22, SW23, SW24, SW25, SW26, SW27, SW28, SW29, SW30, SW31, SW32, SW33, SW34, SW35, SW36, SW37, SW38, SW39, SW40, SW41, SW42, SW43, SW44, SW45, SW46, SW47, SW48, SW49, SW50, SW51, SW52, SW53, SW54, SW55, SW56, SW57, SW58, SW59, SW60, SW61, SW62, SW63, SW64, SW65, SW66, SW67, SW68, SW69, SW70, SW71, SW72, SW73, SW74, SW75, SW76, SW77, SW78, SW79, SW80, SW81: CPG1316S01D02; SW_KEYBOARD_KAIHL-PG1316S

Connections:
KB_SCANMATRIX_CLMN_0: R147.2
KB_SCANMATRIX_CLMN_1: R148.2
KB_SCANMATRIX_CLMN_2: R149.2, R150.2
KB_SCANMATRIX_CLMN_4: R151.2
KB_SCANMATRIX_CLMN_5: R152.2
KB_SCANMATRIX_CLMN_6: R153.2
KB_SCANMATRIX_CLMN_7: R154.2
KB_SCANMATRIX_CLMN_8: R155.2
KB_SCANMATRIX_CLMN_9: R156.2
KB_SCANMATRIX_CLMN_10: R157.2
KB_SCANMATRIX_CLMN_11: R158.2
KB_SCANMATRIX_CLMN_12: R159.2
KB_SCANMATRIX_CLMN_13: R160.2
KB_SCANMATRIX_CLMN_14: R161.2
KB_SCANMATRIX_ROW_0: R162.1
KB_SCANMATRIX_ROW_1: R163.1
KB_SCANMATRIX_ROW_2: R164.1
KB_SCANMATRIX_ROW_3: R165.1
KB_SCANMATRIX_ROW_4: R166.1
KB_SCANMATRIX_ROW_5: R167.1
unnamed: D1.1, D2.1, D3.1, D4.1, D5.1, D6.1, D7.1, D8.1, D9.1, D10.1, D11.1, D12.1, D13.1, D14.1, D15.1, D96.1, R162.2
unnamed: D1.2, SW1.2
unnamed: D2.2, SW2.2
unnamed: D3.2, SW3.2
unnamed: D4.2, SW4.2
unnamed: D5.2, SW5.2
unnamed: D6.2, SW6.2
unnamed: D7.2, SW7.2
unnamed: D8.2, SW8.2
unnamed: D9.2, SW9.2
unnamed: D10.2, SW10.2
unnamed: D11.2, SW11.2
unnamed: D12.2, SW12.2
unnamed: D13.2, SW13.2
unnamed: D14.2, SW14.2
unnamed: D15.2, SW15.2
unnamed: D16.1, D17.1, D18.1, D19.1, D20.1, D21.1, D22.1, D23.1, D24.1, D25.1, D26.1, D27.1, D28.1, D29.1, D97.1, R163.2
unnamed: D16.2, SW16.2
unnamed: D17.2, SW17.2
unnamed: D18.2, SW18.2
unnamed: D19.2, SW19.2
unnamed: D20.2, SW20.2
unnamed: D21.2, SW21.2
unnamed: D22.2, SW22.2
unnamed: D23.2, SW23.2
unnamed: D24.2, SW24.2
unnamed: D25.2, SW25.2
unnamed: D26.2, SW26.2
unnamed: D27.2, SW27.2
unnamed: D28.2, SW28.2
unnamed: D29.2, SW29.2
unnamed: D30.1, D31.1, D32.1, D33.1, D34.1, D35.1, D36.1, D37.1, D38.1, D39.1, D40.1, D41.1, D42.1, D43.1, D98.1, R164.2
unnamed: D30.2, SW30.2
unnamed: D31.2, SW31.2
unnamed: D32.2, SW32.2
unnamed: D33.2, SW33.2
unnamed: D34.2, SW34.2
unnamed: D35.2, SW35.2
unnamed: D36.2, SW36.2
unnamed: D37.2, SW37.2
unnamed: D38.2, SW38.2
unnamed: D39.2, SW39.2
unnamed: D40.2, SW40.2
unnamed: D41.2, SW41.2
unnamed: D42.2, SW42.2
unnamed: D43.2, SW43.2
unnamed: D44.1, D45.1, D46.1, D47.1, D48.1, D49.1, D50.1, D51.1, D52.1, D53.1, D54.1, D55.1, D56.1, D99.1, R165.2
unnamed: D44.2, SW44.2
unnamed: D45.2, SW45.2
unnamed: D46.2, SW46.2
unnamed: D47.2, SW47.2
unnamed: D48.2, SW48.2
unnamed: D49.2, SW49.2
unnamed: D50.2, SW50.2
unnamed: D51.2, SW51.2
unnamed: D52.2, SW52.2
unnamed: D53.2, SW53.2
unnamed: D54.2, SW54.2
unnamed: D55.2, SW55.2
unnamed: D56.2, SW56.2
unnamed: D57.2, SW57.2
unnamed: D58.2, SW58.2
unnamed: D59.2, SW59.2
unnamed: D60.2, SW60.2
unnamed: D61.2, SW61.2
unnamed: D62.2, SW62.2
unnamed: D63.2, SW63.2
unnamed: D64.2, SW64.2
unnamed: D65.2, SW65.2
unnamed: D66.2, SW66.2
unnamed: D67.2, SW67.2
unnamed: D68.2, SW68.2
unnamed: D69.2, SW69.2
unnamed: D70.2, SW70.2
unnamed: D71.2, SW71.2
unnamed: D72.2, SW72.2
unnamed: D73.2, SW73.2
unnamed: D74.2, SW74.2, SW75.2
unnamed: D75.2, SW76.2
unnamed: D76.2, SW77.2
unnamed: D77.2, SW78.2
unnamed: D78.2, SW79.2
unnamed: D79.2, SW80.2
unnamed: D80.2, SW81.2
unnamed: D81.1, R147.1, SW1.1, SW16.1, SW30.1, SW44.1, SW57.1, SW70.1
unnamed: D82.1, R148.1, SW2.1, SW17.1, SW31.1, SW45.1, SW58.1, SW71.1
unnamed: D83.1, R149.1, SW3.1, SW18.1, SW32.1, SW46.1, SW59.1, SW72.1
unnamed: D84.1, R150.1, SW4.1, SW19.1, SW33.1, SW47.1, SW60.1, SW73.1
unnamed: D85.1, R151.1, SW5.1, SW20.1, SW34.1, SW48.1, SW61.1
unnamed: D86.1, R152.1, SW6.1, SW21.1, SW35.1, SW49.1, SW62.1, SW74.1, SW75.1
unnamed: D87.1, R153.1, SW7.1, SW22.1, SW36.1, SW50.1, SW63.1
unnamed: D88.1, R154.1, SW8.1, SW23.1, SW37.1, SW51.1, SW64.1
unnamed: D89.1, R155.1, SW9.1, SW24.1, SW38.1, SW52.1, SW65.1, SW76.1
unnamed: D90.1, R156.1, SW10.1, SW25.1, SW39.1, SW53.1, SW66.1, SW77.1
unnamed: D91.1, R157.1, SW11.1, SW26.1, SW40.1, SW54.1, SW67.1, SW78.1
unnamed: D92.1, R158.1, SW12.1, SW27.1, SW41.1, SW55.1, SW68.1, SW79.1
unnamed: D93.1, R159.1, SW13.1, SW28.1, SW42.1, SW56.1, SW69.1, SW80.1
unnamed: D94.1, R160.1, SW14.1, SW29.1, SW81.1
unnamed: D95.1, R161.1, SW15.1, SW43.1
unnamed: D57.1, D58.1, D59.1, D60.1, D61.1, D62.1, D63.1, D64.1, D65.1, D66.1, D67.1, D68.1, D69.1, D100.1, R166.2
unnamed: D70.1, D71.1, D72.1, D73.1, D74.1, D75.1, D76.1, D77.1, D78.1, D79.1, D80.1, D101.1, R167.2

Notes on the sheet:
KC_P
KC_UP
KC_M
Keycode alignment based on QWERTY layout (eng)
KC_F7
KC_F1
KC_F8
KC_I
KC_S
KC_7
KC_8
KC_CAPS_LOCK
KC_F9
KC_1
KC_U
KC_F6
KC_H
KC_C
KC_4
KC_TAB
KC_9
KC_Y
KC_RIGHT_BRACKET
KC_F12
KC_RIGHT_CTRL
KC_F2
KC_F5
KC_X
KC_F4
KC_6
KC_R
KC_BACKSLASH
KC_SEMICOLON
KC_RIGHT
KC_ENTER
KC_F
KC_LEFT_ALT
KC_T
KC_E
KC_3
KC_N
KC_F11
KC_A
KC_LEFT_SHIFT
KC_ESCAPE
KC_2
KC_DELETE
KC_GRAVE
KC_RIGHT_ALT
KC_SLASH
KC_LEFT_BRACKET
KC_F10
KC_NONUS_HASH
KC_EQUAL
KC_B
KC_J
KC_COMMA
KC_QUOTE
KC_G
KC_F3
KC_O
KC_LEFT
MO(layer)
KC_DOWN
KC_LEFT_CTRL
KC_Z
KC_Q
KC_RIGHT_SHIFT
KC_DOT
KC_L
KC_0
KC_SPACE
KC_D
KC_NO
Specific keyfunctions being implemented in the firmware
KC_W
KC_5
KC_V
KC_K
KC_INSERT
