OV-Tech-GmbH/OVT13/01_Electronics/01_Keyboard/KB-PCB-R02_KiCad/backlight_RGB.kicad_sch

## KiCad design 01_Electronics/01_Keyboard/KB-PCB-R02_KiCad/backlight_RGB.kicad_sch (2024-03-24)

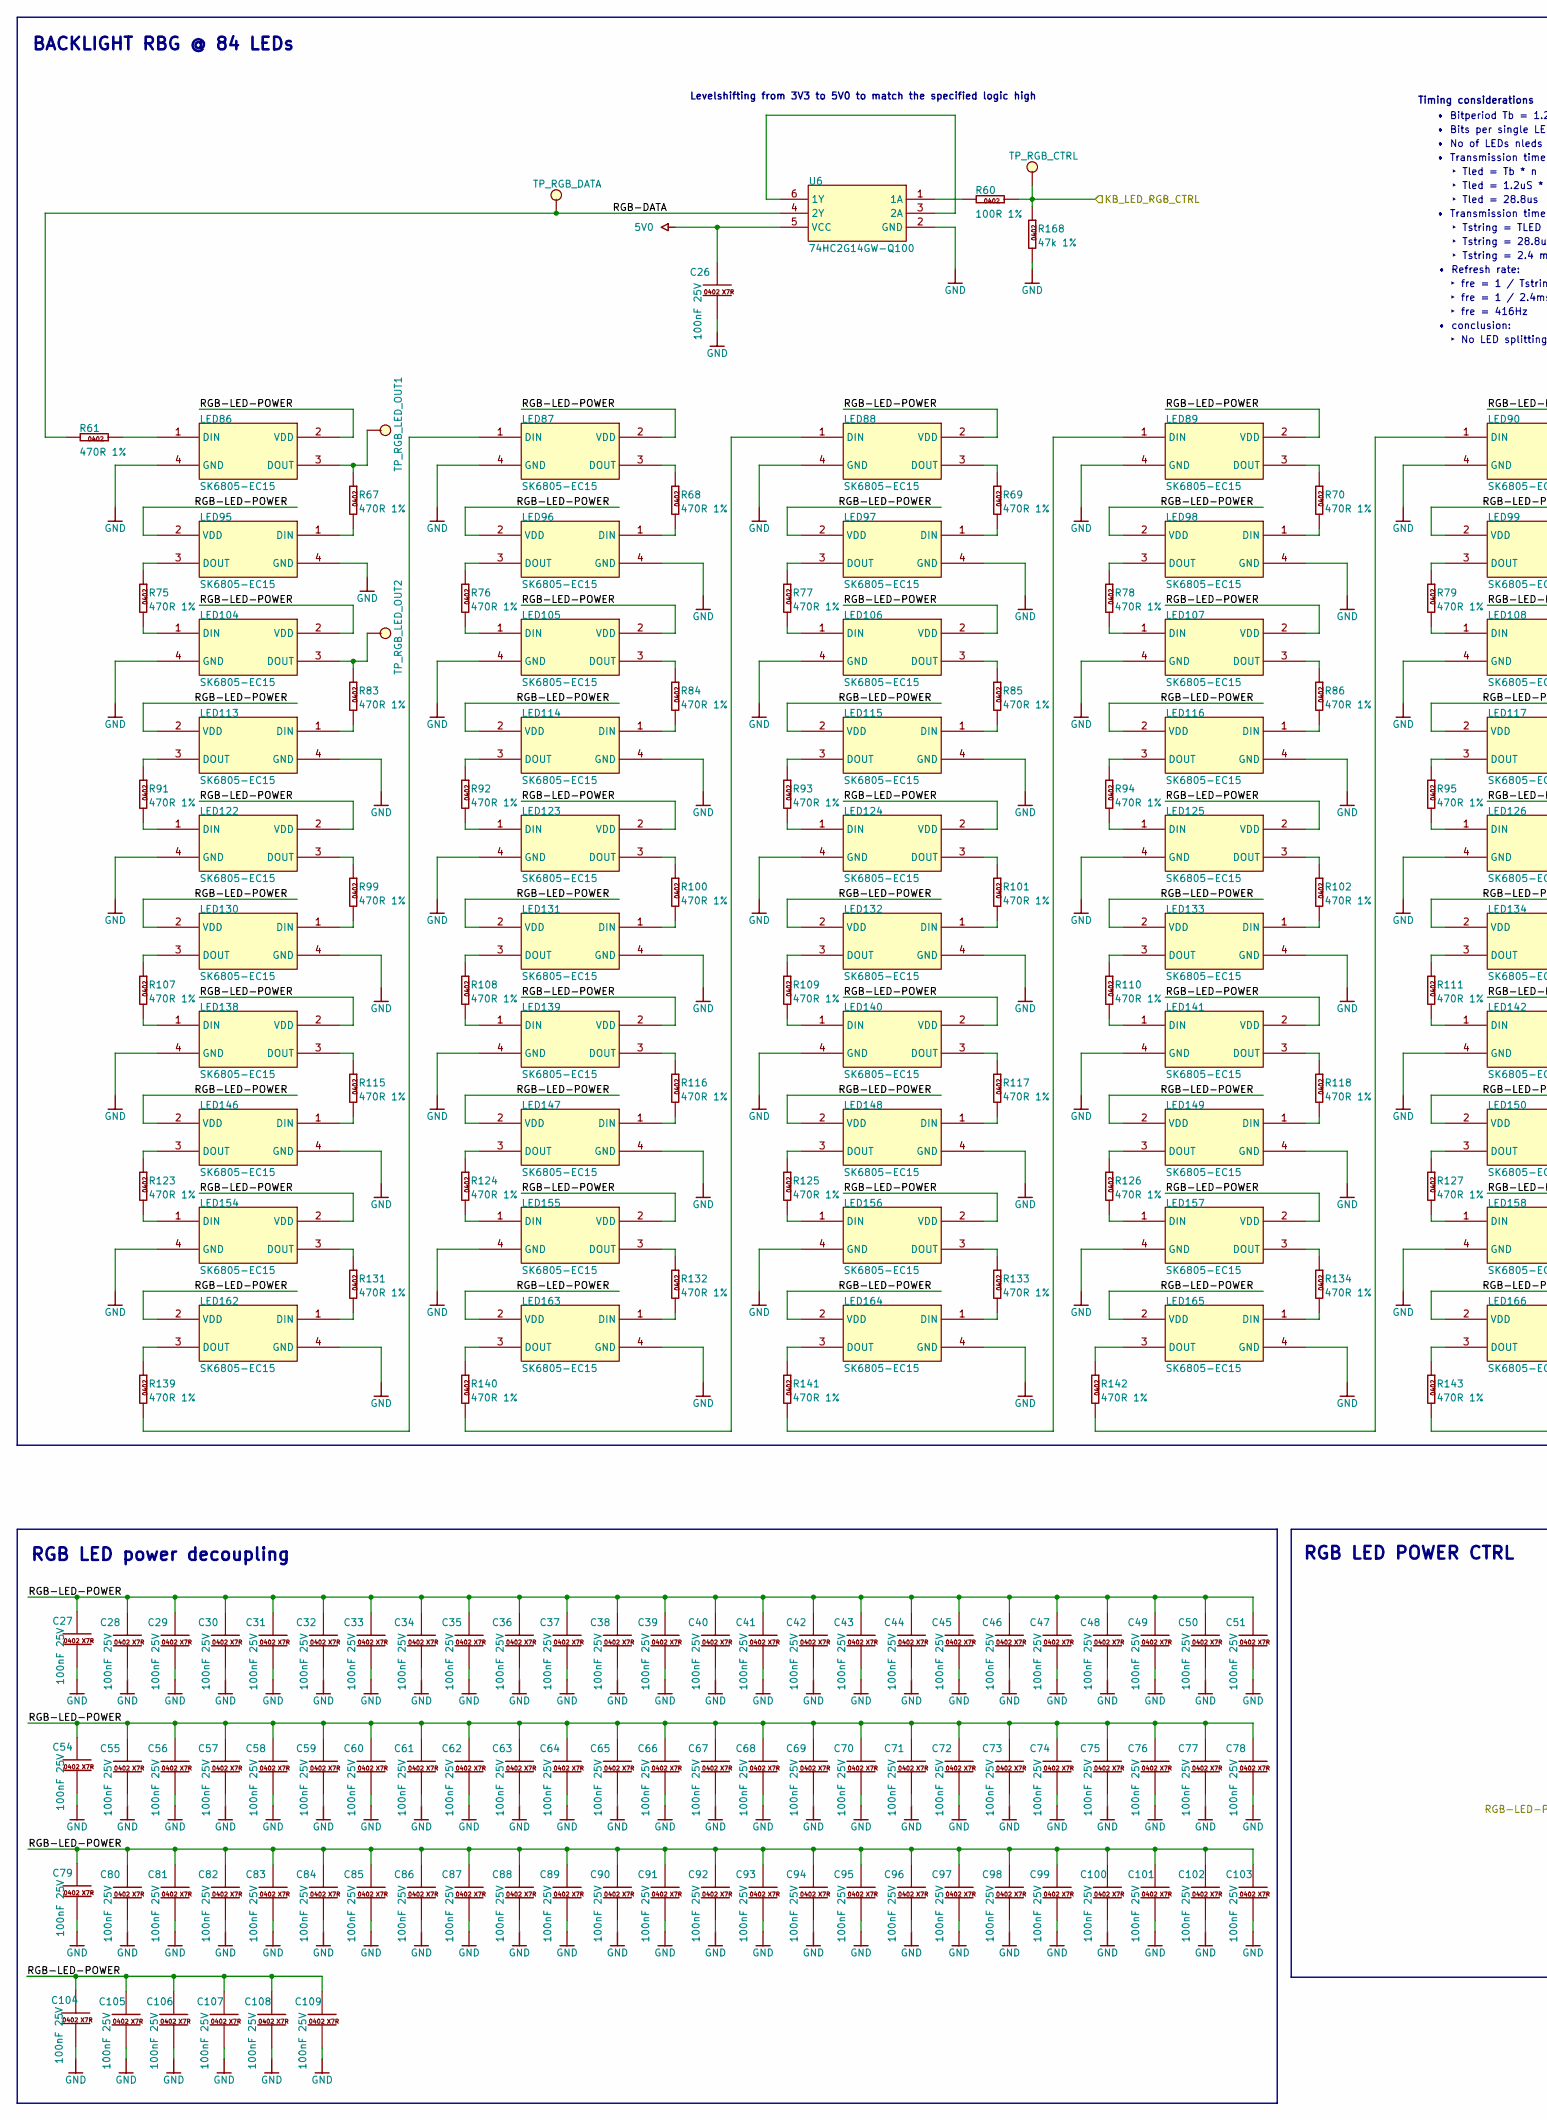
[picture p62: schematic backlight_RGB.kicad_sch, part in row 1, column 1]

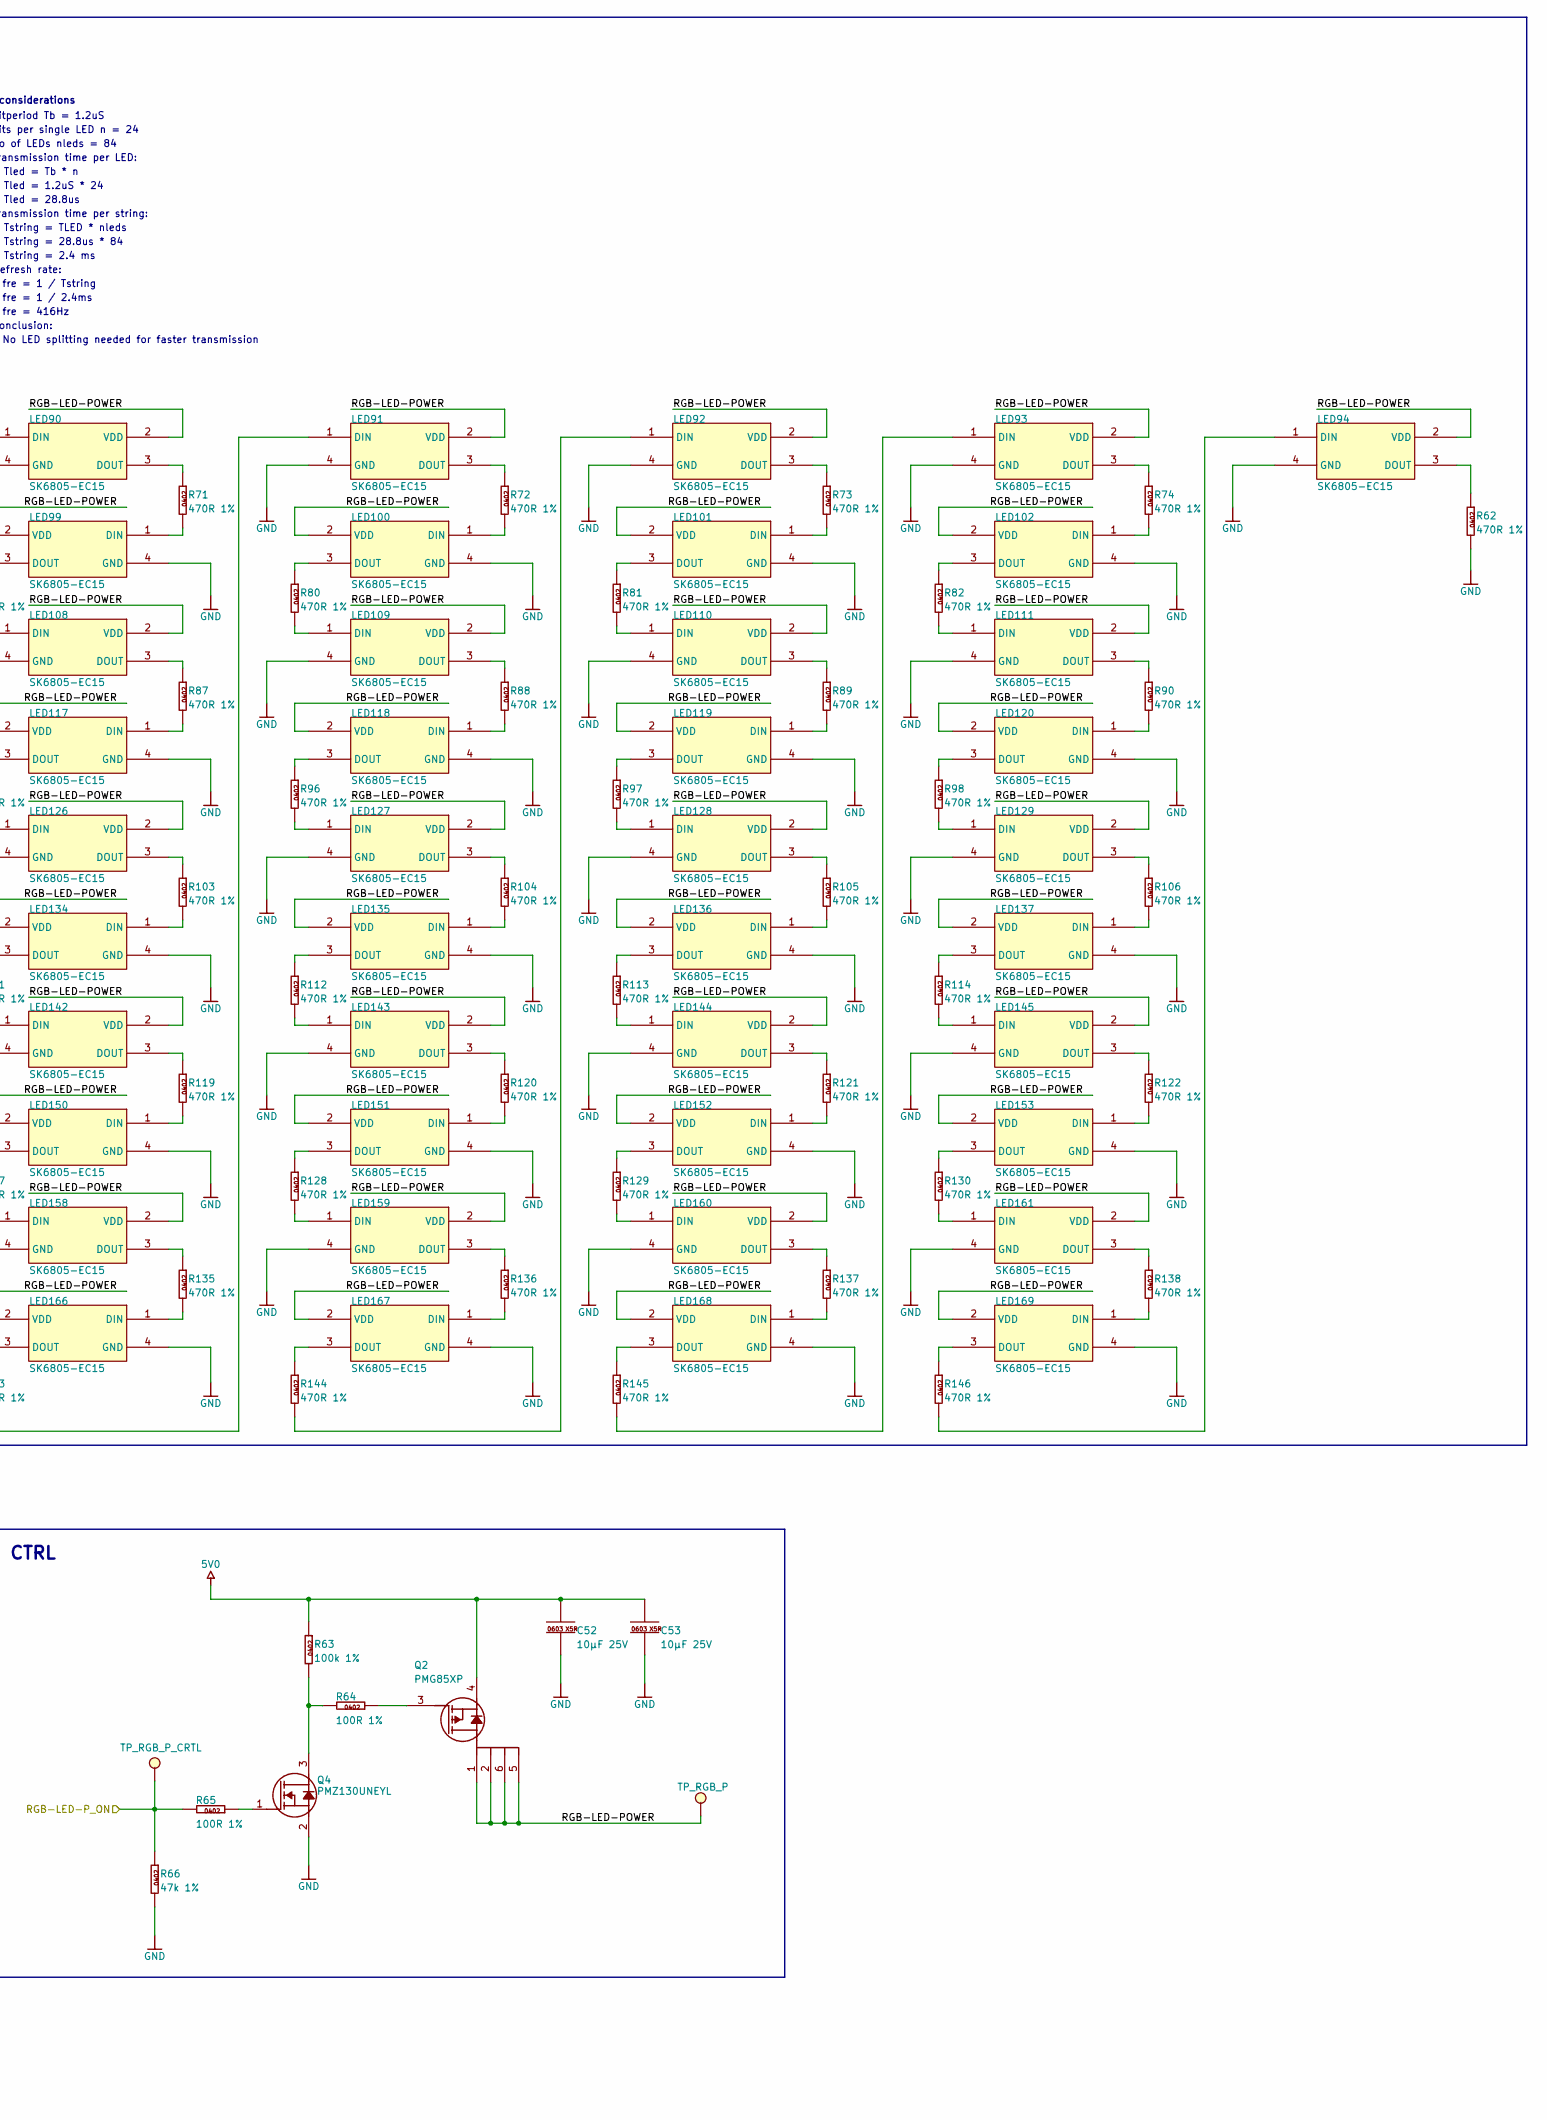
[picture p63: schematic backlight_RGB.kicad_sch, part in row 1, column 2]

Parts:
C26, C27, C28, C29, C30, C31, C32, C33, C34, C35, C36, C37, C38, C39, C40, C41, C42, C43, C44, C45, C46, C47, C48, C49, C50, C51, C54, C55, C56, C57, C58, C59, C60, C61, C62, C63, C64, C65, C66, C67, C68, C69, C70, C71, C72, C73, C74, C75, C76, C77, C78, C79, C80, C81, C82, C83, C84, C85, C86, C87, C88, C89, C90, C91, C92, C93, C94, C95, C96, C97, C98, C99, C100, C101, C102, C103, C104, C105, C106, C107, C108, C109: 100nF 25V; CAPC1005X06L
C52, C53: 10µF 25V; CAPC1608X10L
LED86, LED87, LED88, LED89, LED90, LED91, LED92, LED93, LED94, LED95, LED96, LED97, LED98, LED99, LED100, LED101, LED102, LED104, LED105, LED106, LED107, LED108, LED109, LED110, LED111, LED113, LED114, LED115, LED116, LED117, LED118, LED119, LED120, LED122, LED123, LED124, LED125, LED126, LED127, LED128, LED129, LED130, LED131, LED132, LED133, LED134, LED135, LED136, LED137, LED138, LED139, LED140, LED141, LED142, LED143, LED144, LED145, LED146, LED147, LED148, LED149, LED150, LED151, LED152, LED153, LED154, LED155, LED156, LED157, LED158, LED159, LED160, LED161, LED162, LED163, LED164, LED165, LED166, LED167, LED168, LED169: SK6805-EC15; LED 0606 RGB SK6805-EC15
Q2: PMG85XP; TSOP65P210X110-6N
Q4: PMZ130UNEYL; DFN65P98X50-3N
R60, R64, R65: 100R 1%; RESC1005X04L
R61, R62, R67, R68, R69, R70, R71, R72, R73, R74, R75, R76, R77, R78, R79, R80, R81, R82, R83, R84, R85, R86, R87, R88, R89, R90, R91, R92, R93, R94, R95, R96, R97, R98, R99, R100, R101, R102, R103, R104, R105, R106, R107, R108, R109, R110, R111, R112, R113, R114, R115, R116, R117, R118, R119, R120, R121, R122, R123, R124, R125, R126, R127, R128, R129, R130, R131, R132, R133, R134, R135, R136, R137, R138, R139, R140, R141, R142, R143, R144, R145, R146: 470R 1%; RESC1005X04L
R63: 100k 1%; RESC1005X04L
R66, R168: 47k 1%; RESC1005X04L
TP_RGB_CTRL: Testpoint 0.5mm; TP_0.50mm
TP_RGB_DATA: Testpoint 0.75mm; TP_0.75mm
TP_RGB_LED_OUT1, TP_RGB_LED_OUT2: Testpoint 0.5mm; TP_0.50mm
TP_RGB_P: Testpoint 0.75mm; TP_0.75mm
TP_RGB_P_CRTL: Testpoint 0.75mm; TP_0.75mm
U6: 74HC2G14GW-Q100; TSOP65P210X110-6N

Connections:
KB_LED_RGB_CTRL: R60.2, R168.2, TP_RGB_CTRL.TP
unnamed: C26.1, U6.5 (VCC)
unnamed: C52.1, C53.1, Q2.4 (S), R63.2
unnamed: LED86.1 (DIN), R61.2
unnamed: LED86.3 (DOUT), R67.2, TP_RGB_LED_OUT1.TP
unnamed: LED87.1 (DIN), R139.1
unnamed: LED87.3 (DOUT), R68.2
unnamed: LED88.1 (DIN), R140.1
unnamed: LED88.3 (DOUT), R69.2
unnamed: LED89.1 (DIN), R141.1
unnamed: LED89.3 (DOUT), R70.2
unnamed: LED90.1 (DIN), R142.1
unnamed: LED90.3 (DOUT), R71.2
unnamed: LED91.1 (DIN), R143.1
unnamed: LED91.3 (DOUT), R72.2
unnamed: LED92.1 (DIN), R144.1
unnamed: LED92.3 (DOUT), R73.2
unnamed: LED93.1 (DIN), R145.1
unnamed: LED93.3 (DOUT), R74.2
unnamed: LED94.1 (DIN), R146.1
unnamed: LED94.3 (DOUT), R62.2
unnamed: LED95.1 (DIN), R67.1
unnamed: LED95.3 (DOUT), R75.2
unnamed: LED96.1 (DIN), R68.1
unnamed: LED96.3 (DOUT), R76.2
unnamed: LED97.1 (DIN), R69.1
unnamed: LED97.3 (DOUT), R77.2
unnamed: LED98.1 (DIN), R70.1
unnamed: LED98.3 (DOUT), R78.2
unnamed: LED99.1 (DIN), R71.1
unnamed: LED99.3 (DOUT), R79.2
unnamed: LED100.1 (DIN), R72.1
unnamed: LED100.3 (DOUT), R80.2
unnamed: LED101.1 (DIN), R73.1
unnamed: LED101.3 (DOUT), R81.2
unnamed: LED102.1 (DIN), R74.1
unnamed: LED102.3 (DOUT), R82.2
unnamed: LED104.1 (DIN), R75.1
unnamed: LED104.3 (DOUT), R83.2, TP_RGB_LED_OUT2.TP
unnamed: LED105.1 (DIN), R76.1
unnamed: LED105.3 (DOUT), R84.2
unnamed: LED106.1 (DIN), R77.1
unnamed: LED106.3 (DOUT), R85.2
unnamed: LED107.1 (DIN), R78.1
unnamed: LED107.3 (DOUT), R86.2
unnamed: LED108.1 (DIN), R79.1
unnamed: LED108.3 (DOUT), R87.2
unnamed: LED109.1 (DIN), R80.1
unnamed: LED109.3 (DOUT), R88.2
unnamed: LED110.1 (DIN), R81.1
unnamed: LED110.3 (DOUT), R89.2
unnamed: LED111.1 (DIN), R82.1
unnamed: LED111.3 (DOUT), R90.2
unnamed: LED113.1 (DIN), R83.1
unnamed: LED113.3 (DOUT), R91.2
unnamed: LED114.1 (DIN), R84.1
unnamed: LED114.3 (DOUT), R92.2
unnamed: LED115.1 (DIN), R85.1
unnamed: LED115.3 (DOUT), R93.2
unnamed: LED116.1 (DIN), R86.1
unnamed: LED116.3 (DOUT), R94.2
unnamed: LED117.1 (DIN), R87.1
unnamed: LED117.3 (DOUT), R95.2
unnamed: LED118.1 (DIN), R88.1
unnamed: LED118.3 (DOUT), R96.2
unnamed: LED119.1 (DIN), R89.1
unnamed: LED119.3 (DOUT), R97.2
unnamed: LED120.1 (DIN), R90.1
unnamed: LED120.3 (DOUT), R98.2
unnamed: LED122.1 (DIN), R91.1
unnamed: LED122.3 (DOUT), R99.2
unnamed: LED123.1 (DIN), R92.1
unnamed: LED123.3 (DOUT), R100.2
unnamed: LED124.1 (DIN), R93.1
unnamed: LED124.3 (DOUT), R101.2
unnamed: LED125.1 (DIN), R94.1
unnamed: LED125.3 (DOUT), R102.2
unnamed: LED126.1 (DIN), R95.1
unnamed: LED126.3 (DOUT), R103.2
unnamed: LED127.1 (DIN), R96.1
unnamed: LED127.3 (DOUT), R104.2
unnamed: LED128.1 (DIN), R97.1
unnamed: LED128.3 (DOUT), R105.2
unnamed: LED129.1 (DIN), R98.1
unnamed: LED129.3 (DOUT), R106.2
unnamed: LED130.1 (DIN), R99.1
unnamed: LED130.3 (DOUT), R107.2
unnamed: LED131.1 (DIN), R100.1
unnamed: LED131.3 (DOUT), R108.2
unnamed: LED132.1 (DIN), R101.1
unnamed: LED132.3 (DOUT), R109.2
unnamed: LED133.1 (DIN), R102.1
unnamed: LED133.3 (DOUT), R110.2
unnamed: LED134.1 (DIN), R103.1
unnamed: LED134.3 (DOUT), R111.2
unnamed: LED135.1 (DIN), R104.1
unnamed: LED135.3 (DOUT), R112.2
unnamed: LED136.1 (DIN), R105.1
unnamed: LED136.3 (DOUT), R113.2
unnamed: LED137.1 (DIN), R106.1
unnamed: LED137.3 (DOUT), R114.2
unnamed: LED138.1 (DIN), R107.1
unnamed: LED138.3 (DOUT), R115.2
unnamed: LED139.1 (DIN), R108.1
unnamed: LED139.3 (DOUT), R116.2
unnamed: LED140.1 (DIN), R109.1
unnamed: LED140.3 (DOUT), R117.2
unnamed: LED141.1 (DIN), R110.1
unnamed: LED141.3 (DOUT), R118.2
unnamed: LED142.1 (DIN), R111.1
unnamed: LED142.3 (DOUT), R119.2
unnamed: LED143.1 (DIN), R112.1
unnamed: LED143.3 (DOUT), R120.2
unnamed: LED144.1 (DIN), R113.1
unnamed: LED144.3 (DOUT), R121.2
unnamed: LED145.1 (DIN), R114.1
unnamed: LED145.3 (DOUT), R122.2
unnamed: LED146.1 (DIN), R115.1
unnamed: LED146.3 (DOUT), R123.2
unnamed: LED147.1 (DIN), R116.1
unnamed: LED147.3 (DOUT), R124.2
unnamed: LED148.1 (DIN), R117.1
unnamed: LED148.3 (DOUT), R125.2
unnamed: LED149.1 (DIN), R118.1
unnamed: LED149.3 (DOUT), R126.2
unnamed: LED150.1 (DIN), R119.1
unnamed: LED150.3 (DOUT), R127.2
unnamed: LED151.1 (DIN), R120.1
unnamed: LED151.3 (DOUT), R128.2
unnamed: LED152.1 (DIN), R121.1
unnamed: LED152.3 (DOUT), R129.2
unnamed: LED153.1 (DIN), R122.1
unnamed: LED153.3 (DOUT), R130.2
unnamed: LED154.1 (DIN), R123.1
unnamed: LED154.3 (DOUT), R131.2
unnamed: LED155.1 (DIN), R124.1
unnamed: LED155.3 (DOUT), R132.2
unnamed: LED156.1 (DIN), R125.1
unnamed: LED156.3 (DOUT), R133.2
unnamed: LED157.1 (DIN), R126.1
unnamed: LED157.3 (DOUT), R134.2
unnamed: LED158.1 (DIN), R127.1
unnamed: LED158.3 (DOUT), R135.2
unnamed: LED159.1 (DIN), R128.1
unnamed: LED159.3 (DOUT), R136.2
unnamed: LED160.1 (DIN), R129.1
unnamed: LED160.3 (DOUT), R137.2
unnamed: LED161.1 (DIN), R130.1
unnamed: LED161.3 (DOUT), R138.2
unnamed: LED162.1 (DIN), R131.1
unnamed: LED162.3 (DOUT), R139.2
unnamed: LED163.1 (DIN), R132.1
unnamed: LED163.3 (DOUT), R140.2
unnamed: LED164.1 (DIN), R133.1
unnamed: LED164.3 (DOUT), R141.2
unnamed: LED165.1 (DIN), R134.1
unnamed: LED165.3 (DOUT), R142.2
unnamed: LED166.1 (DIN), R135.1
unnamed: LED166.3 (DOUT), R143.2
unnamed: LED167.1 (DIN), R136.1
unnamed: LED167.3 (DOUT), R144.2
unnamed: LED168.1 (DIN), R137.1
unnamed: LED168.3 (DOUT), R145.2
unnamed: LED169.1 (DIN), R138.1
unnamed: LED169.3 (DOUT), R146.2
unnamed: Q2.3 (G), R64.2
unnamed: Q4.1 (G), R65.2
unnamed: Q4.3 (D), R63.1, R64.1
unnamed: R60.1, U6.1 (1A)
unnamed: U6.3 (2A), U6.6 (1Y)
RGB-DATA: R61.1, TP_RGB_DATA.TP, U6.4 (2Y)
RGB-LED-POWER: C27.1, C28.1, C29.1, C30.1, C31.1, C32.1, C33.1, C34.1, C35.1, C36.1, C37.1, C38.1, C39.1, C40.1, C41.1, C42.1, C43.1, C44.1, C45.1, C46.1, C47.1, C48.1, C49.1, C50.1, C51.1, C54.1, C55.1, C56.1, C57.1, C58.1, C59.1, C60.1, C61.1, C62.1, C63.1, C64.1, C65.1, C66.1, C67.1, C68.1, C69.1, C70.1, C71.1, C72.1, C73.1, C74.1, C75.1, C76.1, C77.1, C78.1, C79.1, C80.1, C81.1, C82.1, C83.1, C84.1, C85.1, C86.1, C87.1, C88.1, C89.1, C90.1, C91.1, C92.1, C93.1, C94.1, C95.1, C96.1, C97.1, C98.1, C99.1, C100.1, C101.1, C102.1, C103.1, C104.1, C105.1, C106.1, C107.1, C108.1, C109.1, LED86.2 (VDD), LED87.2 (VDD), LED88.2 (VDD), LED89.2 (VDD), LED90.2 (VDD), LED91.2 (VDD), LED92.2 (VDD), LED93.2 (VDD), LED94.2 (VDD), LED95.2 (VDD), LED96.2 (VDD), LED97.2 (VDD), LED98.2 (VDD), LED99.2 (VDD), LED100.2 (VDD), LED101.2 (VDD), LED102.2 (VDD), LED104.2 (VDD), LED105.2 (VDD), LED106.2 (VDD), LED107.2 (VDD), LED108.2 (VDD), LED109.2 (VDD), LED110.2 (VDD), LED111.2 (VDD), LED113.2 (VDD), LED114.2 (VDD), LED115.2 (VDD), LED116.2 (VDD), LED117.2 (VDD), LED118.2 (VDD), LED119.2 (VDD), LED120.2 (VDD), LED122.2 (VDD), LED123.2 (VDD), LED124.2 (VDD), LED125.2 (VDD), LED126.2 (VDD), LED127.2 (VDD), LED128.2 (VDD), LED129.2 (VDD), LED130.2 (VDD), LED131.2 (VDD), LED132.2 (VDD), LED133.2 (VDD), LED134.2 (VDD), LED135.2 (VDD), LED136.2 (VDD), LED137.2 (VDD), LED138.2 (VDD), LED139.2 (VDD), LED140.2 (VDD), LED141.2 (VDD), LED142.2 (VDD), LED143.2 (VDD), LED144.2 (VDD), LED145.2 (VDD), LED146.2 (VDD), LED147.2 (VDD), LED148.2 (VDD), LED149.2 (VDD), LED150.2 (VDD), LED151.2 (VDD), LED152.2 (VDD), LED153.2 (VDD), LED154.2 (VDD), LED155.2 (VDD), LED156.2 (VDD), LED157.2 (VDD), LED158.2 (VDD), LED159.2 (VDD), LED160.2 (VDD), LED161.2 (VDD), LED162.2 (VDD), LED163.2 (VDD), LED164.2 (VDD), LED165.2 (VDD), LED166.2 (VDD), LED167.2 (VDD), LED168.2 (VDD), LED169.2 (VDD), Q2.1 (D), Q2.2 (D), Q2.5 (D), Q2.6 (D), TP_RGB_P.TP
RGB-LED-P_ON: R65.1, R66.2, TP_RGB_P_CRTL.TP

Notes on the sheet:
• Bits per single LED n = 24
‣ fre = 416Hz
‣ Tled = 28.8us
RGB LED POWER CTRL
‣ Tled = 1.2uS * 24
BACKLIGHT RBG @ 84 LEDs
‣ fre = 1 / 2.4ms
‣ fre = 1 / Tstring
• No of LEDs nleds = 84
‣ Tstring = 28.8us * 84
‣ No LED splitting needed for faster transmission
RGB LED power decoupling
‣ Tled = Tb * n
• Transmission time per string:
‣ Tstring = 2.4 ms
• Refresh rate:
Timing considerations
• conclusion:
• Bitperiod Tb = 1.2uS
‣ Tstring = TLED * nleds
• Transmission time per LED:
Levelshifting from 3V3 to 5V0 to match the specified logic high
